Board-Folk/Einstein-TC-01/Kicad/einstein_addressing.kicad_sch

## KiCad design Kicad/einstein_addressing.kicad_sch (2025-11-02)

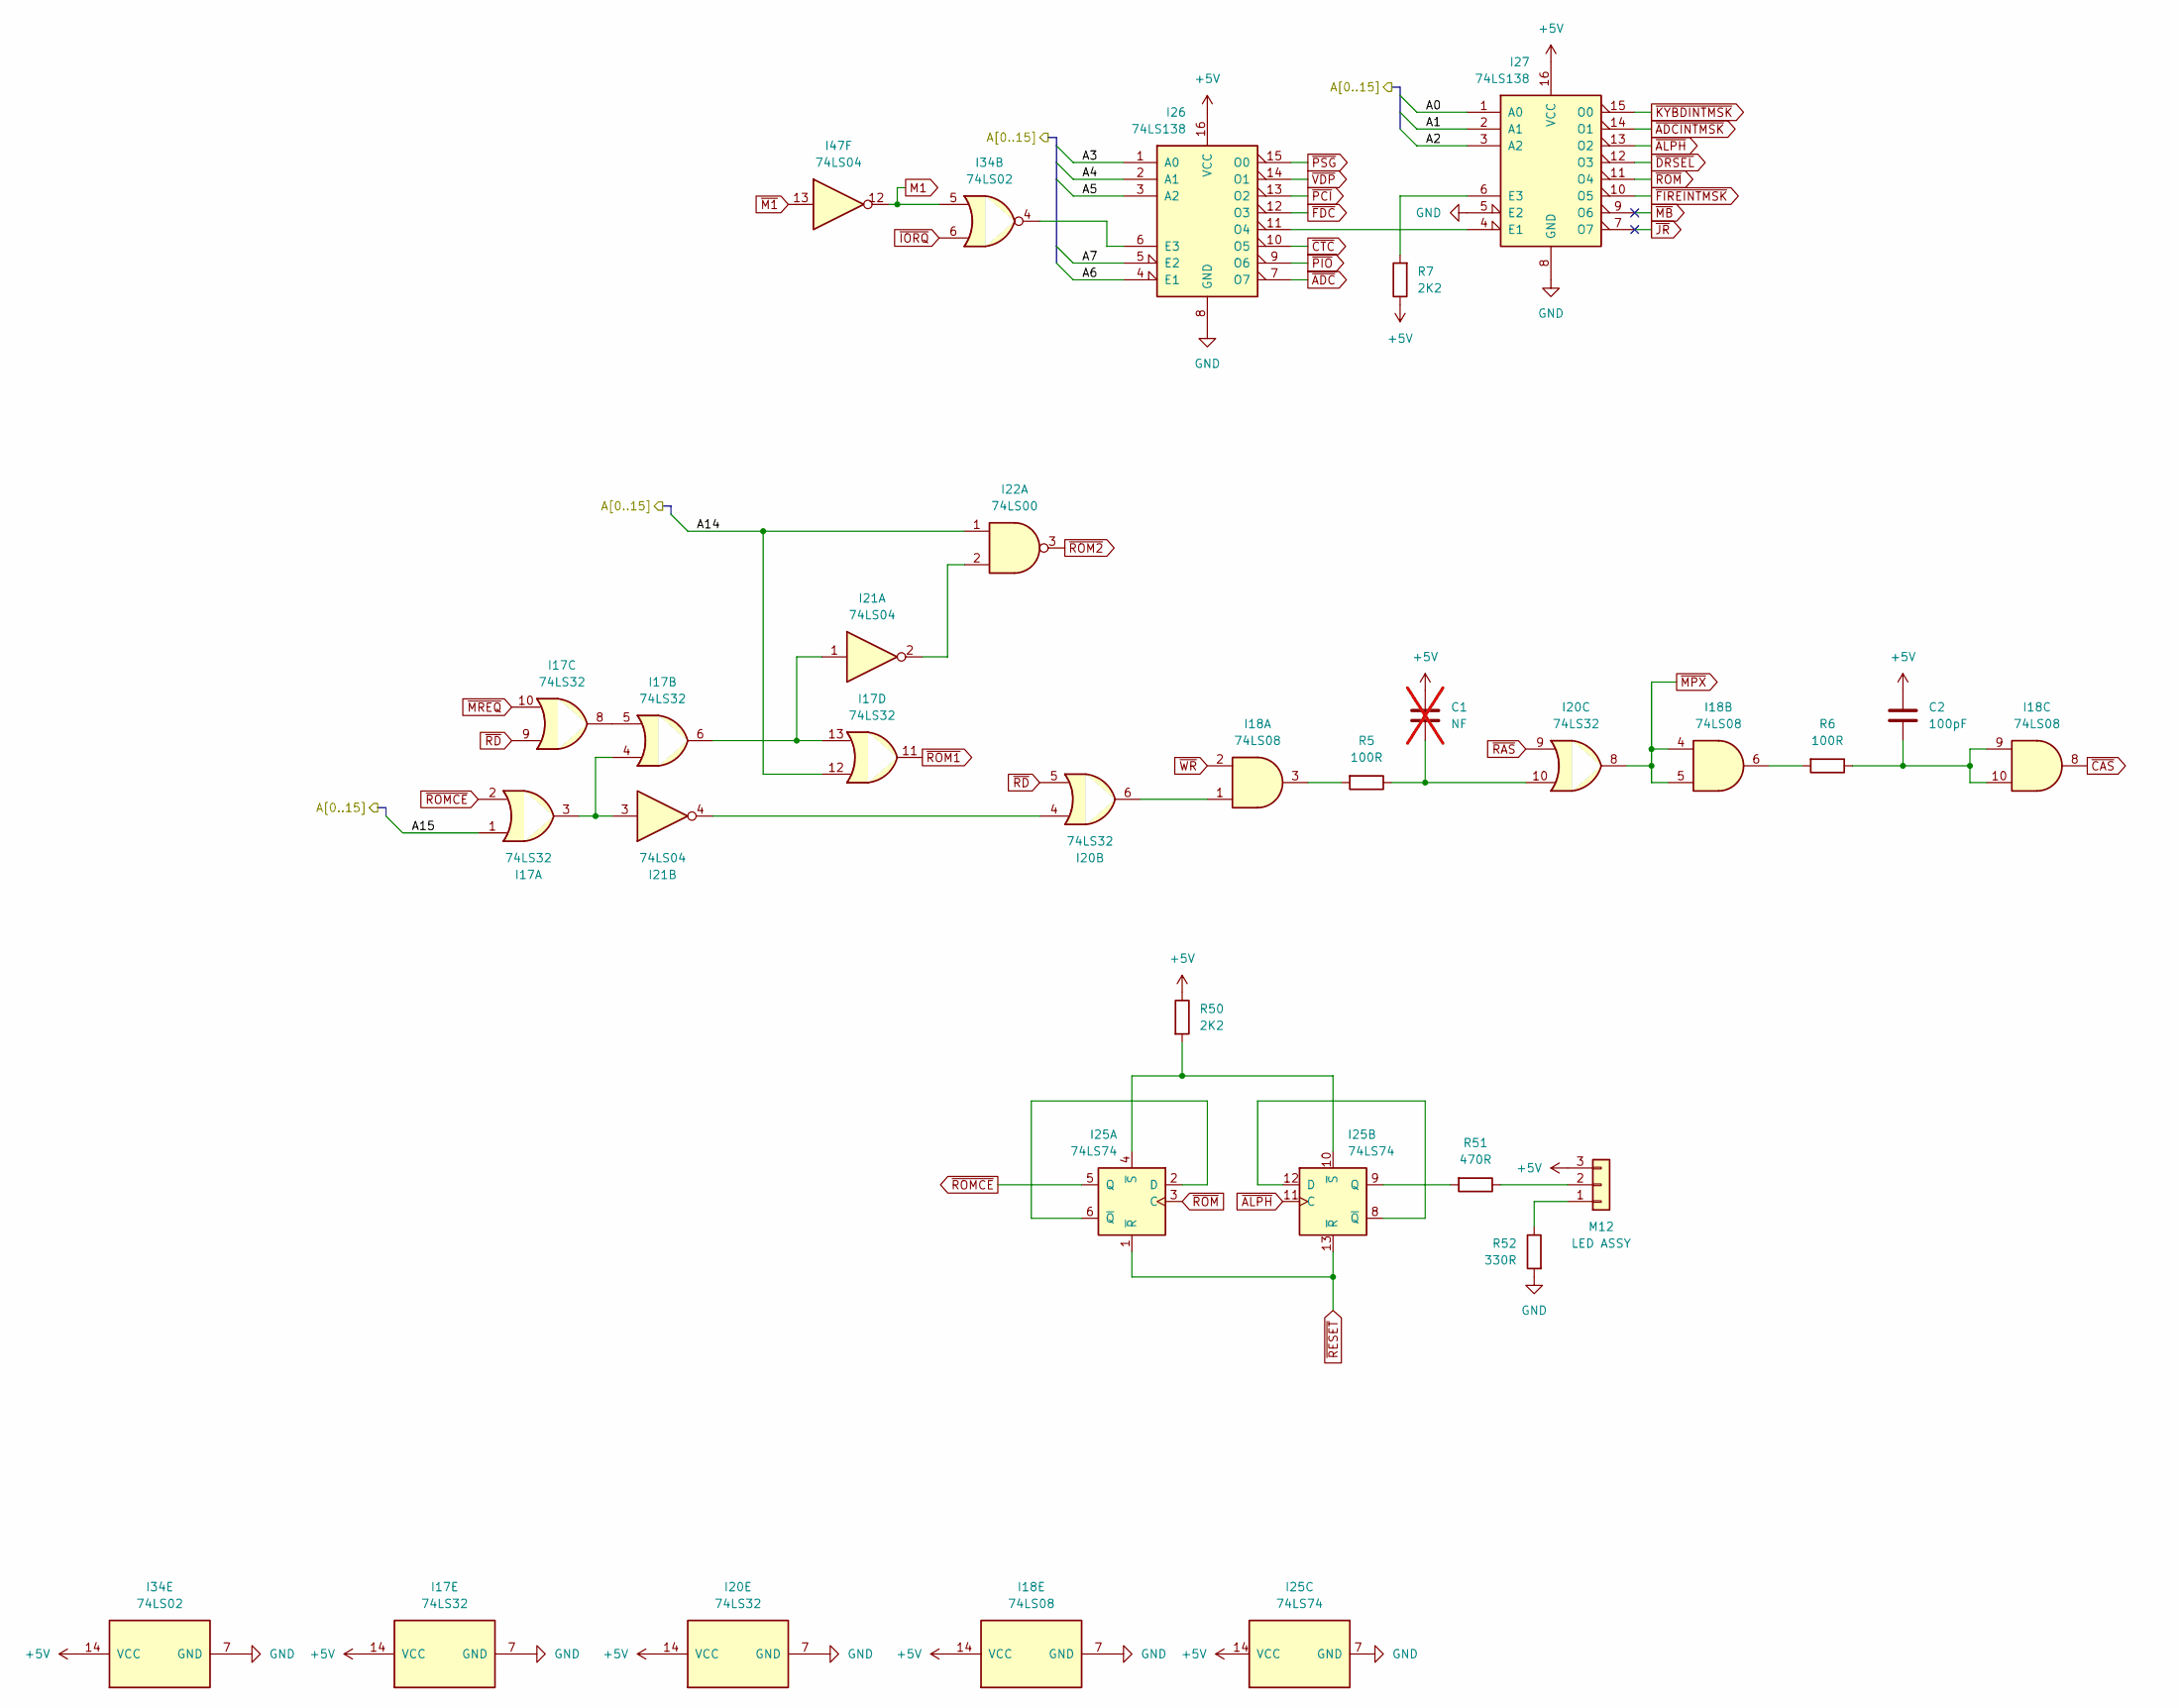
[picture p41: schematic einstein_addressing.kicad_sch]

Parts:
C1: NF; C_Disc_10.16mm; not fitted
C2: 100pF; C_Disc_10.16mm
I17, I20: 74LS32; DIP-14_W7.62mm
I18: 74LS08; DIP-14_W7.62mm
I21, I47: 74LS04; DIP-14_W7.62mm
I22: 74LS00; DIP-14_W7.62mm
I25: 74LS74; DIP-14_W7.62mm
I26, I27: 74LS138; DIP-16_W7.62mm
I34: 74LS02; DIP-14_W7.62mm
M12: LED ASSY; M12 PinHeader_1x03_P2.54mm
R5, R6: 100R; Resistor 12.70mm
R7, R50: 2K2; Resistor 12.70mm
R51: 470R; Resistor 12.70mm
R52: 330R; Resistor 12.70mm

Connections:
+5V: C1.1, C2.1, I17.14 (VCC), I18.14 (VCC), I20.14 (VCC), I25.14 (VCC), I26.16 (VCC), I27.16 (VCC), I34.14 (VCC), M12.3, R7.1, R50.1
A0: I27.1 (A0)
A1: I27.2 (A1)
A2: I27.3 (A2)
A3: I26.1 (A0)
A4: I26.2 (A1)
A5: I26.3 (A2)
A6: I26.4 (E1)
A7: I26.5 (E2)
A14: I17.12, I22.1
A15: I17.1
GND: I17.7 (GND), I18.7 (GND), I20.7 (GND), I25.7 (GND), I26.8 (GND), I27.5 (E2), I27.8 (GND), I34.7 (GND), R52.2
M1: I34.5, I47.12
unnamed: C1.2, I20.10, R5.1
unnamed: C2.2, I18.9, I18.10, R6.1
unnamed: I17.3, I17.4, I21.3
unnamed: I17.5, I17.8
unnamed: I17.6, I17.13, I21.1
unnamed: I18.1, I20.6
unnamed: I18.3, R5.2
unnamed: I18.6, R6.2
unnamed: I20.4, I21.4
unnamed: I21.2, I22.2
unnamed: I25.2 (D), I25.6 (~Q)
unnamed: I25.9 (Q), R51.2
unnamed: I25.4 (~S), I25.10 (~S), R50.2
unnamed: I25.8 (~Q), I25.12 (D)
unnamed: I26.6 (E3), I34.4
unnamed: I26.11 (O4), I27.4 (E1)
unnamed: I27.6 (E3), R7.2
unnamed: M12.1, R52.1
unnamed: M12.2, R51.1
~ADCINTMSK: I27.14 (O1)
~ADC: I26.7 (O7)
~ALPH: I25.11 (C), I27.13 (O2)
~CAS: I18.8
~CTC: I26.10 (O5)
~DRSEL: I27.12 (O3)
~FDC: I26.12 (O3)
~FIREINTMSK: I27.10 (O5)
~IORQ: I34.6
~JR: I27.7 (O7)
~KYBDINTMSK: I27.15 (O0)
~M1: I47.13
~MB: I27.9 (O6)
~MPX: I18.4, I18.5, I20.8
~MREQ: I17.10
~PCI: I26.13 (O2)
~PIO: I26.9 (O6)
~PSG: I26.15 (O0)
~RAS: I20.9
~RD: I17.9, I20.5
~RESET: I25.1 (~R), I25.13 (~R)
~ROM1: I17.11
~ROM2: I22.3
~ROMCE: I17.2, I25.5 (Q)
~ROM: I25.3 (C), I27.11 (O4)
~VDP: I26.14 (O1)
~WR: I18.2
