Board-Folk/Einstein-TC-01/Kicad/einstein_cpu.kicad_sch

## KiCad design Kicad/einstein_cpu.kicad_sch (2026-03-14)

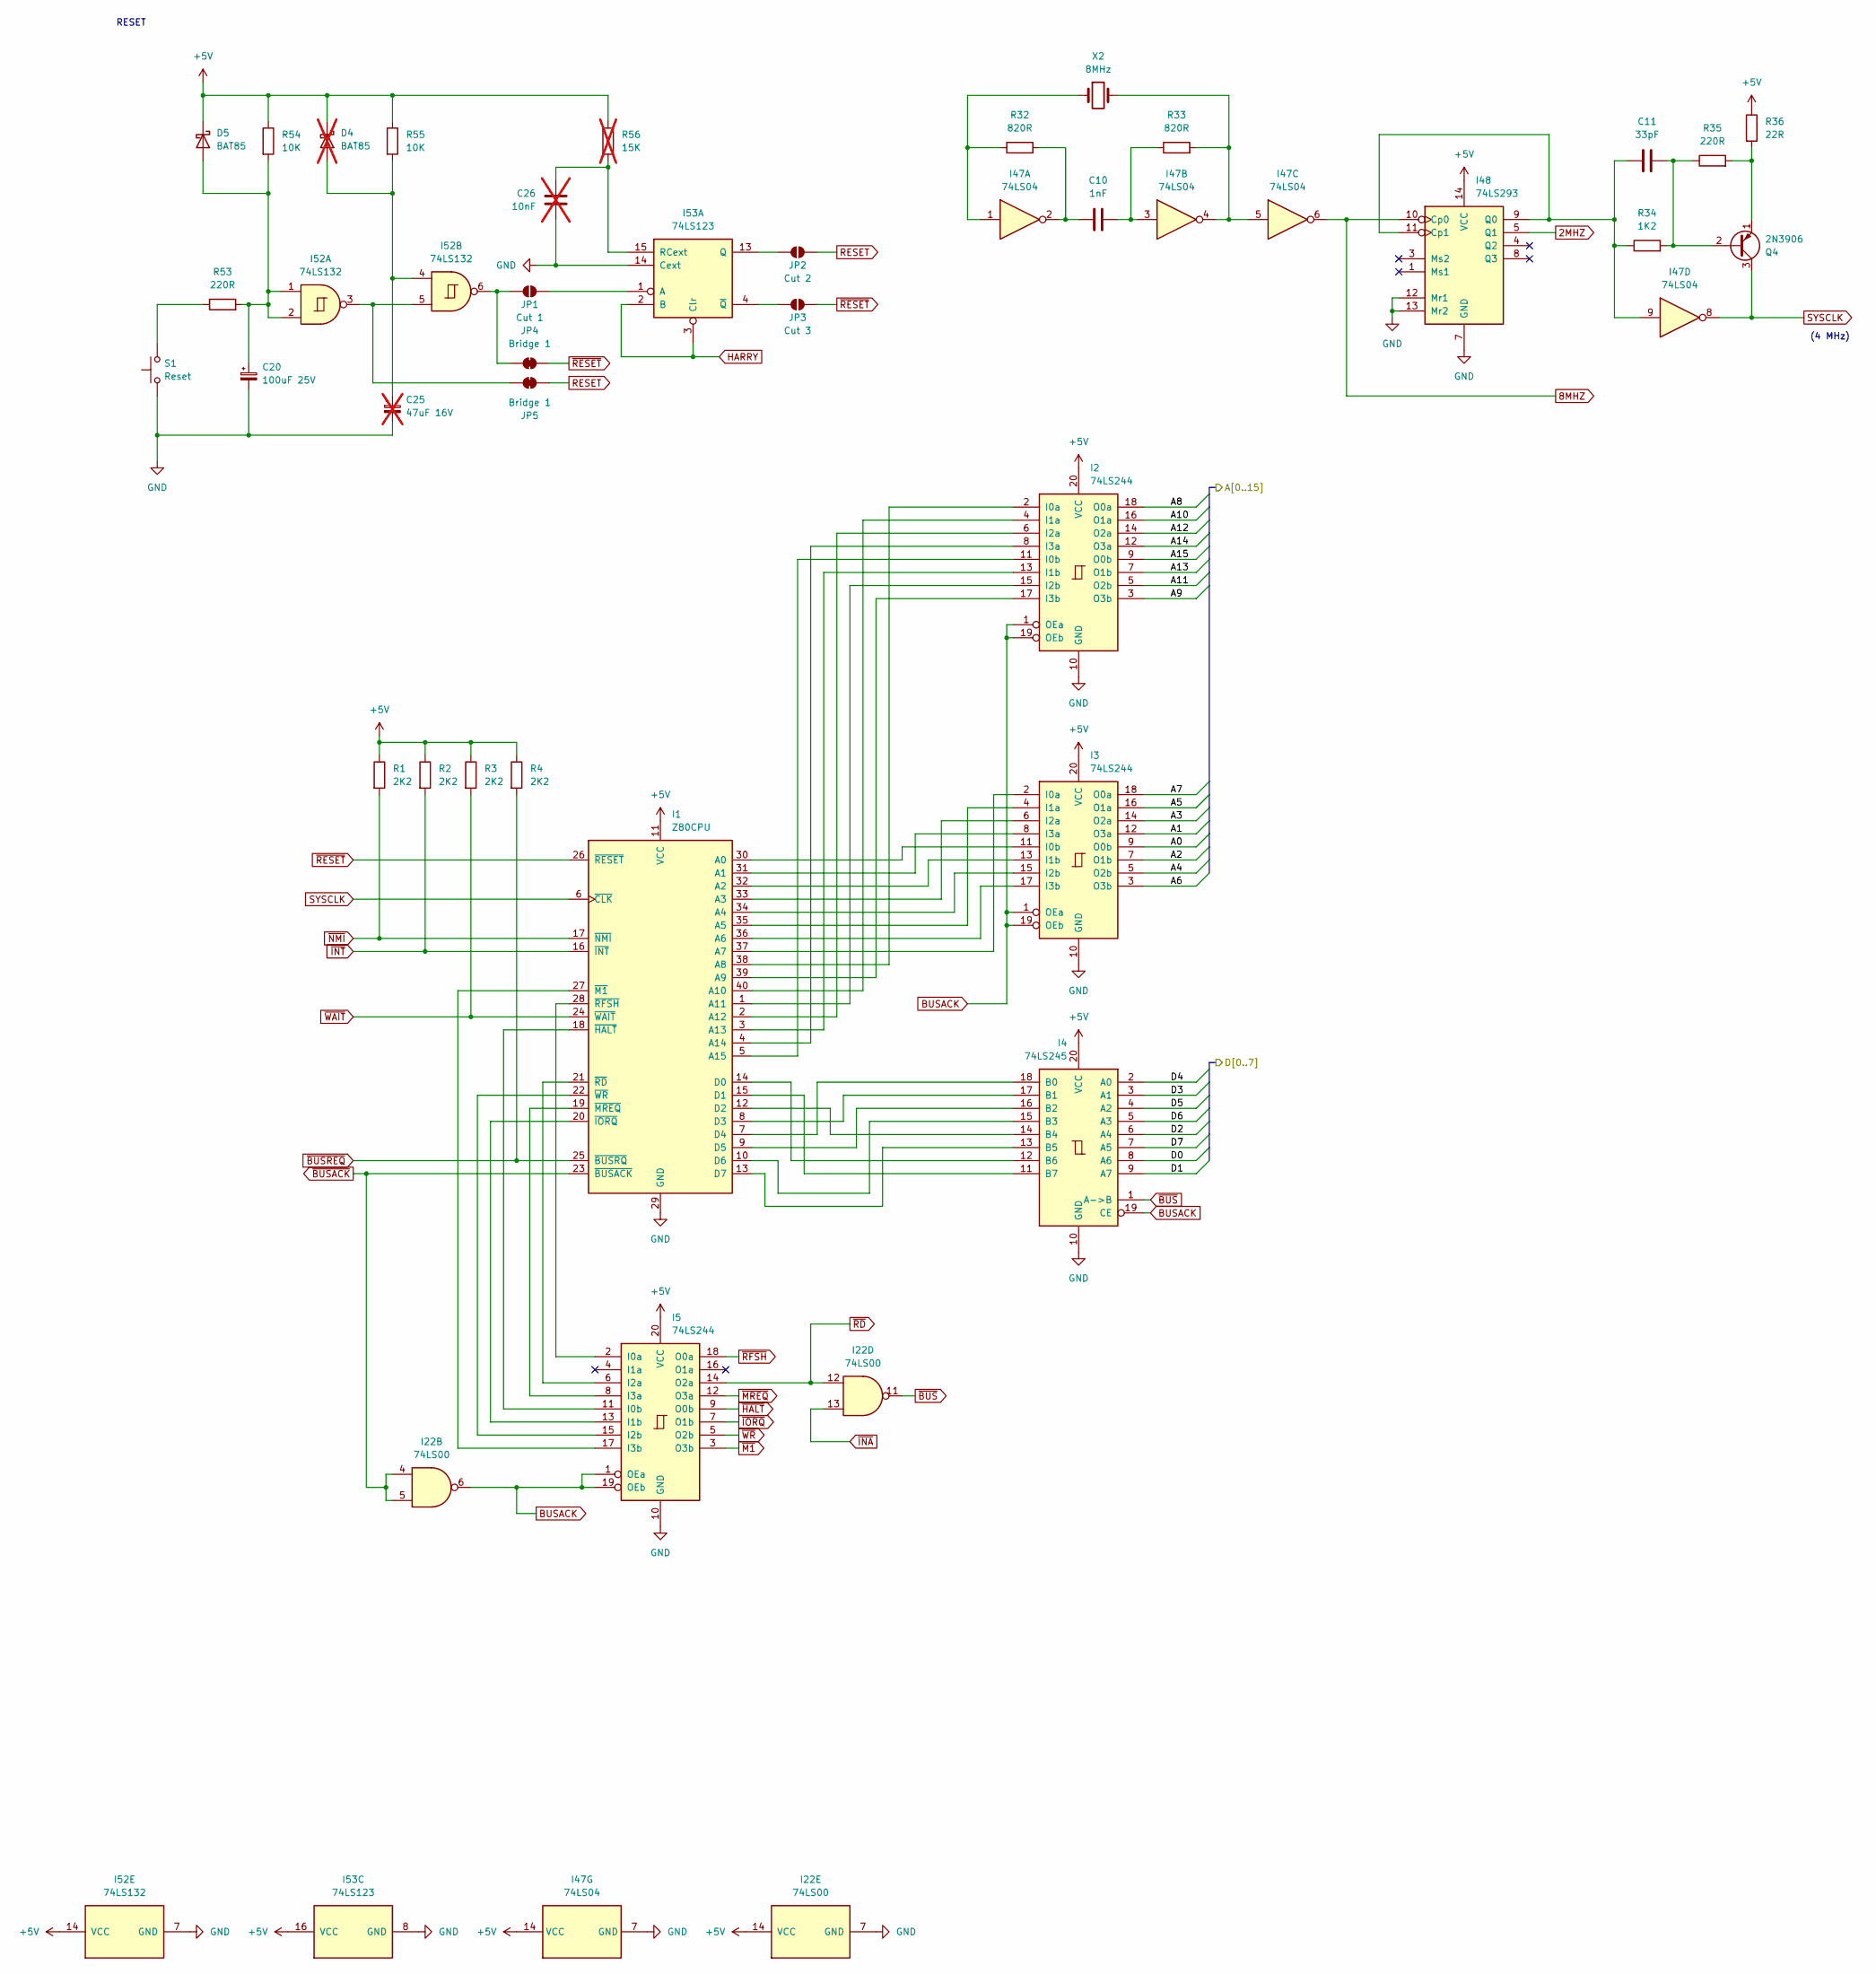
[picture p42: schematic einstein_cpu.kicad_sch]

Parts:
C10: 1nF; C_Disc_12.7mm
C11: 33pF; C_Disc_12.7mm
C20: 100uF 25V; Elec_5.08mm - Box
C25: 47uF 16V; Elec_5.08mm - Box; not fitted
C26: 10nF; C_Disc_12.7mm; not fitted
D4: BAT85; Diode 10.16mm; not fitted
D5: BAT85; Diode 10.16mm
I1: Z80CPU; DIP-40_W15.24mm
I2, I3, I5: 74LS244; DIP-20_W7.62mm
I4: 74LS245; DIP-20_W7.62mm
I22: 74LS00; DIP-14_W7.62mm
I47: 74LS04; DIP-14_W7.62mm
I48: 74LS293; DIP-14_W7.62mm
I52: 74LS132; DIP-14_W7.62mm
I53: 74LS123; DIP-16_W7.62mm
JP1: Cut 1; Bodge Cut
JP2: Cut 2; Bodge Cut
JP3: Cut 3; Bodge Cut
JP4, JP5: Bridge 1; Bodge Bridge
Q4: 2N3906; Transistor - Box 1 (Alt 1+3) No corner marking
R1, R2, R3, R4: 2K2; Resistor 12.70mm
R32, R33: 820R; Resistor 12.70mm
R34: 1K2; Resistor 12.70mm
R35, R53: 220R; Resistor 12.70mm
R36: 22R; Resistor 12.70mm
R54, R55: 10K; Resistor 12.70mm
R56: 15K; Resistor 12.70mm; not fitted
S1: Reset
X2: 8MHz; Crystal

Connections:
2MHZ: I48.5 (Q1)
8MHZ: I47.6, I48.10 (Cp0)
+5V: D4.1 (K), D5.1 (K), I1.11 (VCC), I2.20 (VCC), I3.20 (VCC), I4.20 (VCC), I5.20 (VCC), I22.14 (VCC), I47.14 (VCC), I48.14 (VCC), I52.14 (VCC), I53.16 (VCC), R1.1, R2.1, R3.1, R4.1, R36.1, R54.1, R55.1, R56.1
A0: I3.9 (O0b)
A1: I3.12 (O3a)
A2: I3.7 (O1b)
A3: I3.14 (O2a)
A4: I3.5 (O2b)
A5: I3.16 (O1a)
A6: I3.3 (O3b)
A7: I3.18 (O0a)
A8: I2.18 (O0a)
A9: I2.3 (O3b)
A10: I2.16 (O1a)
A11: I2.5 (O2b)
A12: I2.14 (O2a)
A13: I2.7 (O1b)
A14: I2.12 (O3a)
A15: I2.9 (O0b)
BUSACK: I2.1 (OEa), I2.19 (OEb), I3.1 (OEa), I3.19 (OEb), I4.19 (CE), I5.1 (OEa), I5.19 (OEb), I22.6
D0: I4.8 (A6)
D1: I4.9 (A7)
D2: I4.6 (A4)
D3: I4.3 (A1)
D4: I4.2 (A0)
D5: I4.4 (A2)
D6: I4.5 (A3)
D7: I4.7 (A5)
GND: C20.2, C25.2, C26.2, I1.29 (GND), I2.10 (GND), I3.10 (GND), I4.10 (GND), I5.10 (GND), I22.7 (GND), I47.7 (GND), I48.7 (GND), I48.12 (Mr1), I48.13 (Mr2), I52.7 (GND), I53.8 (GND), I53.14 (Cext), S1.1
HARRY: I53.2 (B), I53.3 (Clr)
unnamed: C10.1, I47.3, R33.1
unnamed: C10.2, I47.2, R32.2
unnamed: C11.1, Q4.2 (B), R34.2, R35.1
unnamed: C11.2, I47.9, I48.9 (Q0), I48.11 (Cp1), R34.1
unnamed: C20.1, D5.2 (A), I52.1, I52.2, R53.2, R54.2
unnamed: C25.1, D4.2 (A), I52.4, R55.2
unnamed: C26.1, I53.15 (RCext), R56.2
unnamed: I1.1 (A11), I2.15 (I2b)
unnamed: I1.2 (A12), I2.6 (I2a)
unnamed: I1.3 (A13), I2.13 (I1b)
unnamed: I1.4 (A14), I2.8 (I3a)
unnamed: I1.5 (A15), I2.11 (I0b)
unnamed: I1.7 (D4), I4.18 (B0)
unnamed: I1.8 (D3), I4.17 (B1)
unnamed: I1.9 (D5), I4.16 (B2)
unnamed: I1.10 (D6), I4.15 (B3)
unnamed: I1.12 (D2), I4.14 (B4)
unnamed: I1.13 (D7), I4.13 (B5)
unnamed: I1.14 (D0), I4.12 (B6)
unnamed: I1.15 (D1), I4.11 (B7)
unnamed: I1.18 (~HALT), I5.11 (I0b)
unnamed: I1.19 (~MREQ), I5.8 (I3a)
unnamed: I1.20 (~IORQ), I5.13 (I1b)
unnamed: I1.21 (~RD), I5.6 (I2a)
unnamed: I1.22 (~WR), I5.15 (I2b)
unnamed: I1.27 (~M1), I5.17 (I3b)
unnamed: I1.28 (~RFSH), I5.2 (I0a)
unnamed: I1.30 (A0), I3.11 (I0b)
unnamed: I1.31 (A1), I3.8 (I3a)
unnamed: I1.32 (A2), I3.13 (I1b)
unnamed: I1.33 (A3), I3.6 (I2a)
unnamed: I1.34 (A4), I3.15 (I2b)
unnamed: I1.35 (A5), I3.4 (I1a)
unnamed: I1.36 (A6), I3.17 (I3b)
unnamed: I1.37 (A7), I3.2 (I0a)
unnamed: I1.38 (A8), I2.2 (I0a)
unnamed: I1.39 (A9), I2.17 (I3b)
unnamed: I1.40 (A10), I2.4 (I1a)
unnamed: I47.1, R32.1, X2.1
unnamed: I47.4, I47.5, R33.2, X2.2
unnamed: I52.3, I52.5, JP5.1 (A)
unnamed: I52.6, JP1.1 (A), JP4.1 (A)
unnamed: I53.1 (A), JP1.2 (B)
unnamed: I53.4 (~Q), JP3.1 (A)
unnamed: I53.13 (Q), JP2.1 (A)
unnamed: Q4.1 (E), R35.2, R36.2
unnamed: R53.1, S1.2
RESET: JP2.2 (B), JP5.2 (B)
SYSCLK: I1.6 (~CLK), I47.8, Q4.3 (C)
~BUSACK: I1.23 (~BUSACK), I22.4, I22.5
~BUSREQ: I1.25 (~BUSRQ), R4.2
~BUS: I4.1 (A->B), I22.11
~HALT: I5.9 (O0b)
~INA: I22.13
~INT: I1.16 (~INT), R2.2
~IORQ: I5.7 (O1b)
~M1: I5.3 (O3b)
~MREQ: I5.12 (O3a)
~NMI: I1.17 (~NMI), R1.2
~RD: I5.14 (O2a), I22.12
~RESET: I1.26 (~RESET), JP3.2 (B), JP4.2 (B)
~RFSH: I5.18 (O0a)
~WAIT: I1.24 (~WAIT), R3.2
~WR: I5.5 (O2b)

Notes on the sheet:
(4 MHz)
RESET
