Board-Folk/Einstein-TC-01/Kicad/einstein_fdd.kicad_sch

## KiCad design Kicad/einstein_fdd.kicad_sch (2025-11-02)

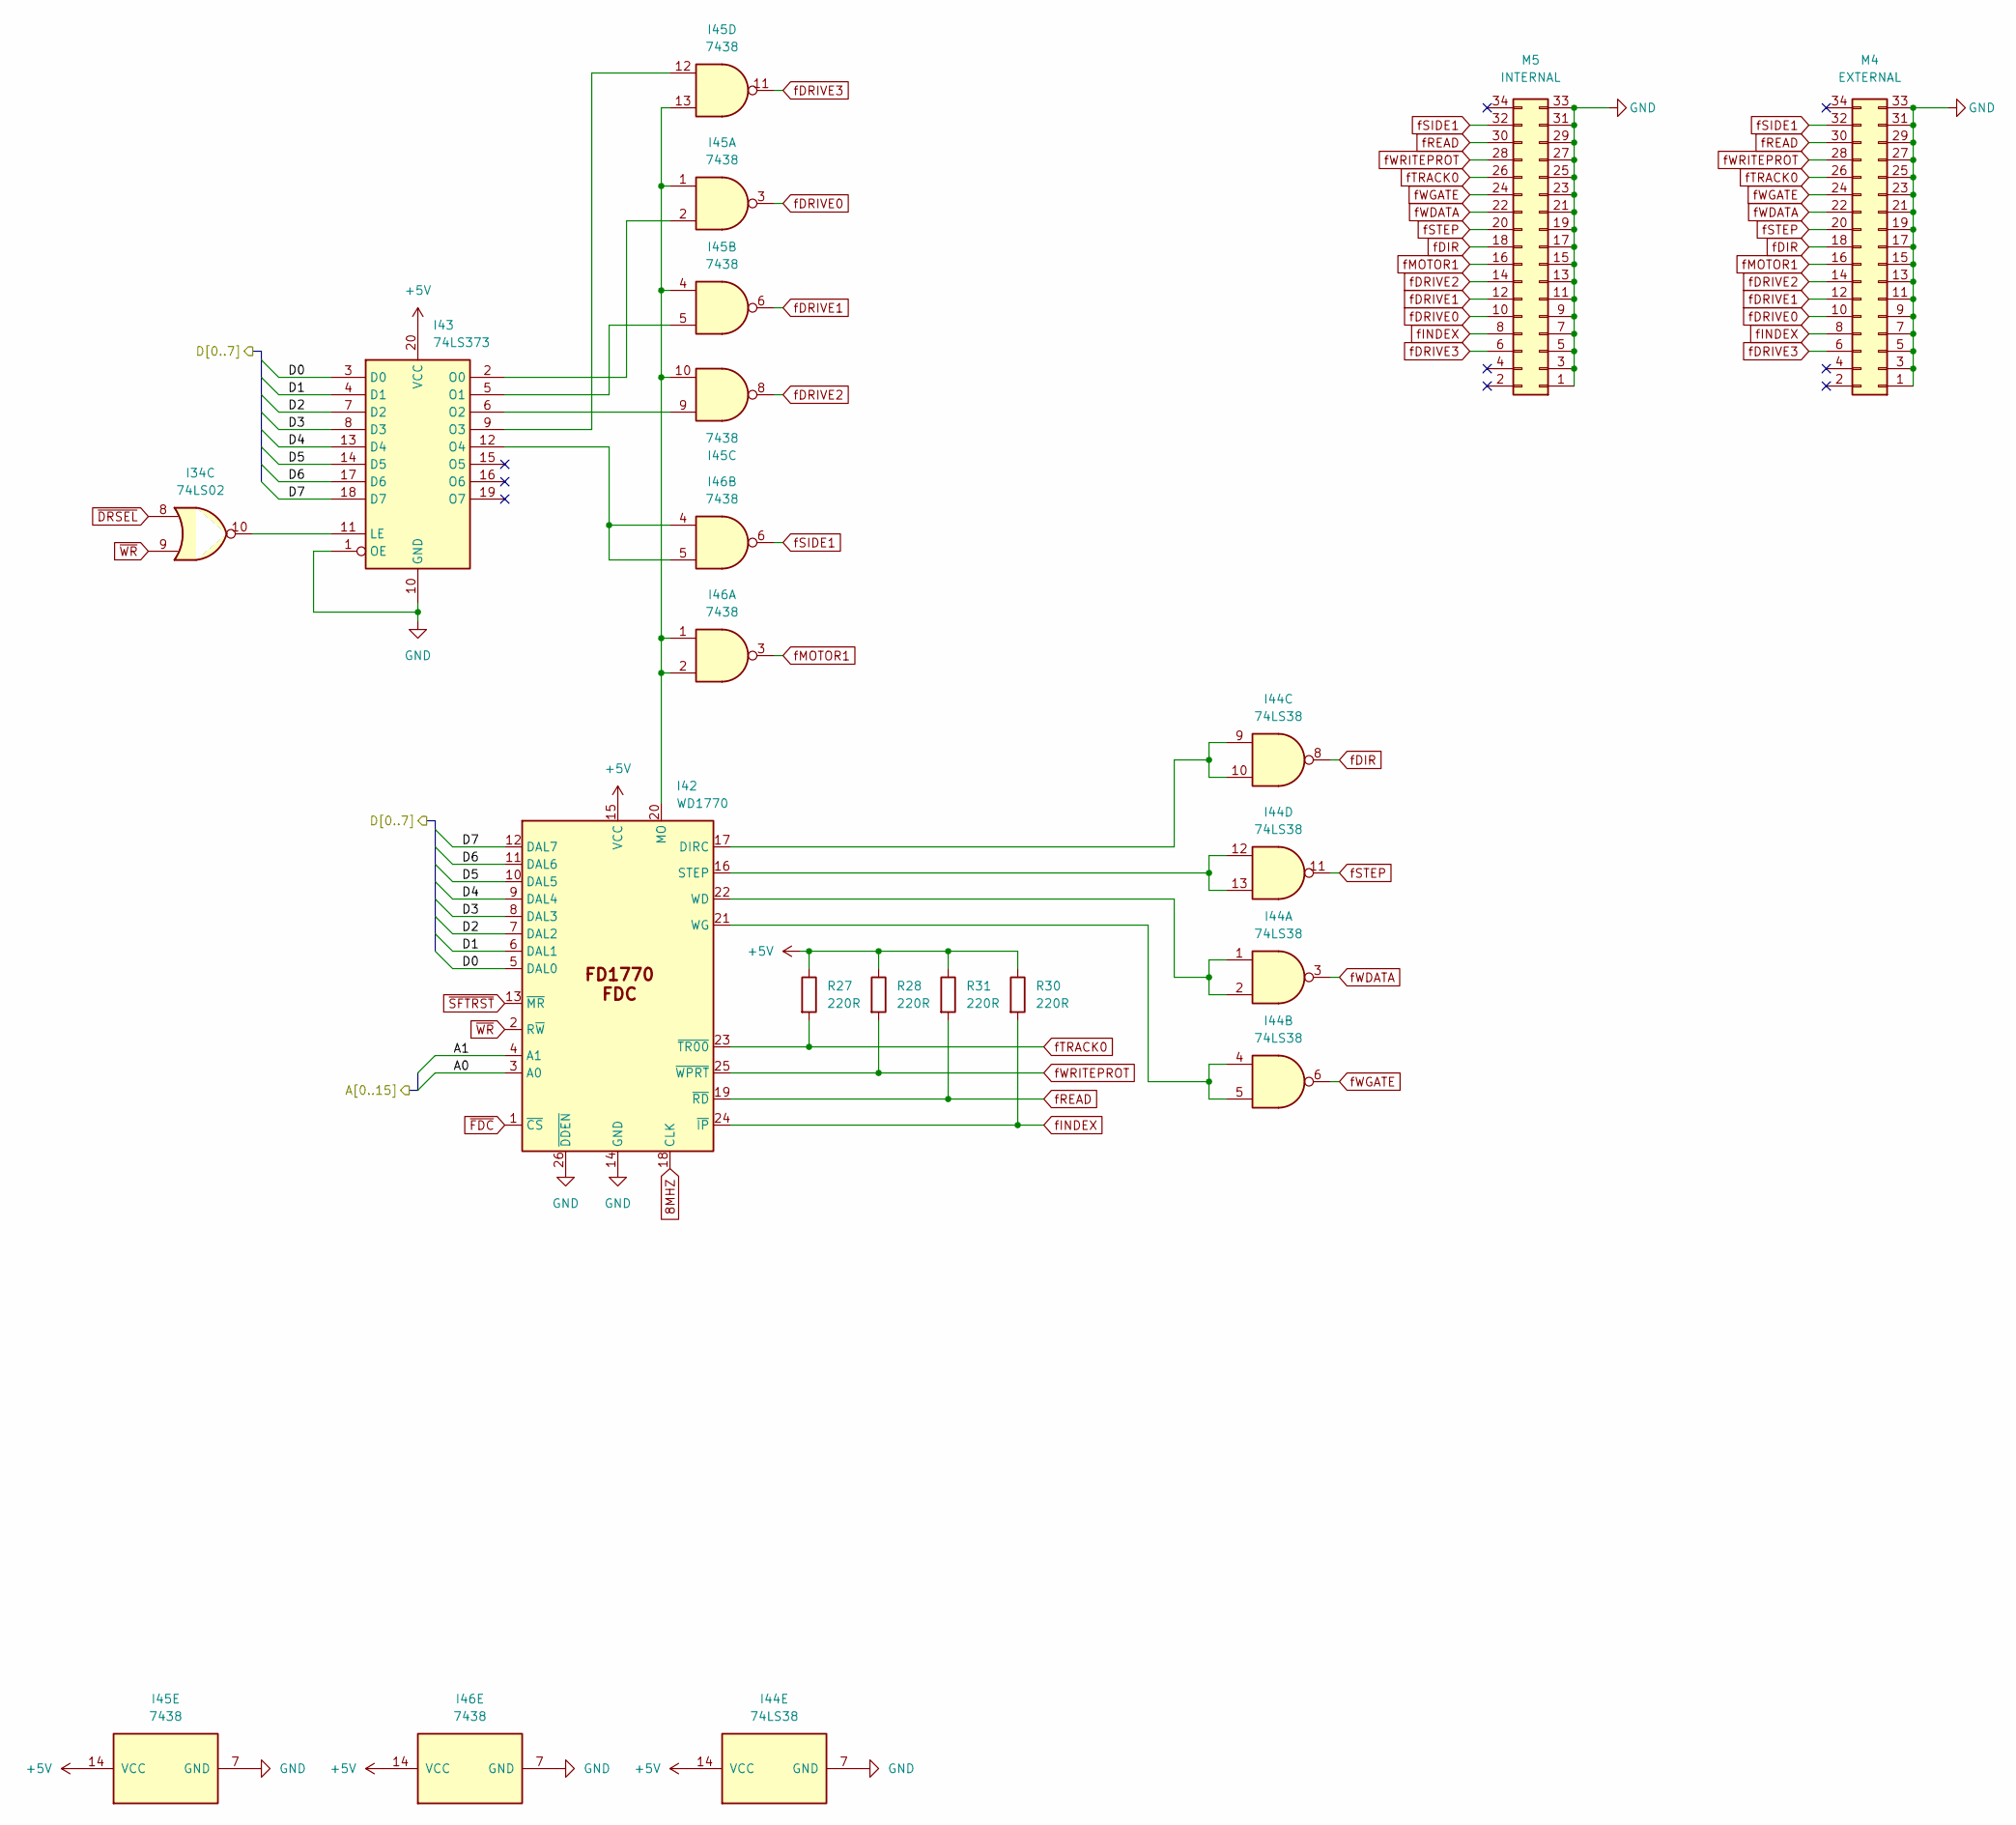
[picture p43: schematic einstein_fdd.kicad_sch]

Parts:
I34: 74LS02; DIP-14_W7.62mm
I42: WD1770; DIP-28_W15.24mm
I43: 74LS373; DIP-20_W7.62mm
I44: 74LS38; DIP-14_W7.62mm
I45, I46: 7438; DIP-14_W7.62mm
M4: EXTERNAL; PinHeader_2x17_P2.54mm
M5: INTERNAL; PinHeader_2x17_P2.54mm
R27, R28, R30, R31: 220R; Resistor 12.70mm

Connections:
8MHZ: I42.18 (CLK)
+5V: I42.15 (VCC), I43.20 (VCC), I44.14 (VCC), I45.14 (VCC), I46.14 (VCC), R27.1, R28.1, R30.1, R31.1
A0: I42.3 (A0)
A1: I42.4 (A1)
D0: I42.5 (DAL0), I43.3 (D0)
D1: I42.6 (DAL1), I43.4 (D1)
D2: I42.7 (DAL2), I43.7 (D2)
D3: I42.8 (DAL3), I43.8 (D3)
D4: I42.9 (DAL4), I43.13 (D4)
D5: I42.10 (DAL5), I43.14 (D5)
D6: I42.11 (DAL6), I43.17 (D6)
D7: I42.12 (DAL7), I43.18 (D7)
GND: I42.14 (GND), I42.26 (~DDEN), I43.1 (OE), I43.10 (GND), I44.7 (GND), I45.7 (GND), I46.7 (GND), M4.1, M4.3, M4.5, M4.7, M4.9, M4.11, M4.13, M4.15, M4.17, M4.19, M4.21, M4.23, M4.25, M4.27, M4.29, M4.31, M4.33, M5.1, M5.3, M5.5, M5.7, M5.9, M5.11, M5.13, M5.15, M5.17, M5.19, M5.21, M5.23, M5.25, M5.27, M5.29, M5.31, M5.33
unnamed: I34.10, I43.11 (LE)
unnamed: I42.16 (STEP), I44.12, I44.13
unnamed: I42.17 (DIRC), I44.9, I44.10
unnamed: I42.20 (MO), I45.1, I45.4, I45.10, I45.13, I46.1, I46.2
unnamed: I42.21 (WG), I44.4, I44.5
unnamed: I42.22 (WD), I44.1, I44.2
unnamed: I43.2 (O0), I45.2
unnamed: I43.5 (O1), I45.5
unnamed: I43.6 (O2), I45.9
unnamed: I43.9 (O3), I45.12
unnamed: I43.12 (O4), I46.4, I46.5
fDIR: I44.8, M4.18, M5.18
fDRIVE0: I45.3, M4.10, M5.10
fDRIVE1: I45.6, M4.12, M5.12
fDRIVE2: I45.8, M4.14, M5.14
fDRIVE3: I45.11, M4.6, M5.6
fINDEX: I42.24 (~IP), M4.8, M5.8, R30.2
fMOTOR1: I46.3, M4.16, M5.16
fREAD: I42.19 (~RD), M4.30, M5.30, R31.2
fSIDE1: I46.6, M4.32, M5.32
fSTEP: I44.11, M4.20, M5.20
fTRACK0: I42.23 (~TR00), M4.26, M5.26, R27.2
fWDATA: I44.3, M4.22, M5.22
fWGATE: I44.6, M4.24, M5.24
fWRITEPROT: I42.25 (~WPRT), M4.28, M5.28, R28.2
~DRSEL: I34.8
~FDC: I42.1 (~CS)
~SFTRST: I42.13 (~MR)
~WR: I34.9, I42.2 (R~W)
