Board-Folk/Einstein-TC-01/Kicad/einstein_memory.kicad_sch

## KiCad design Kicad/einstein_memory.kicad_sch (2025-11-02)

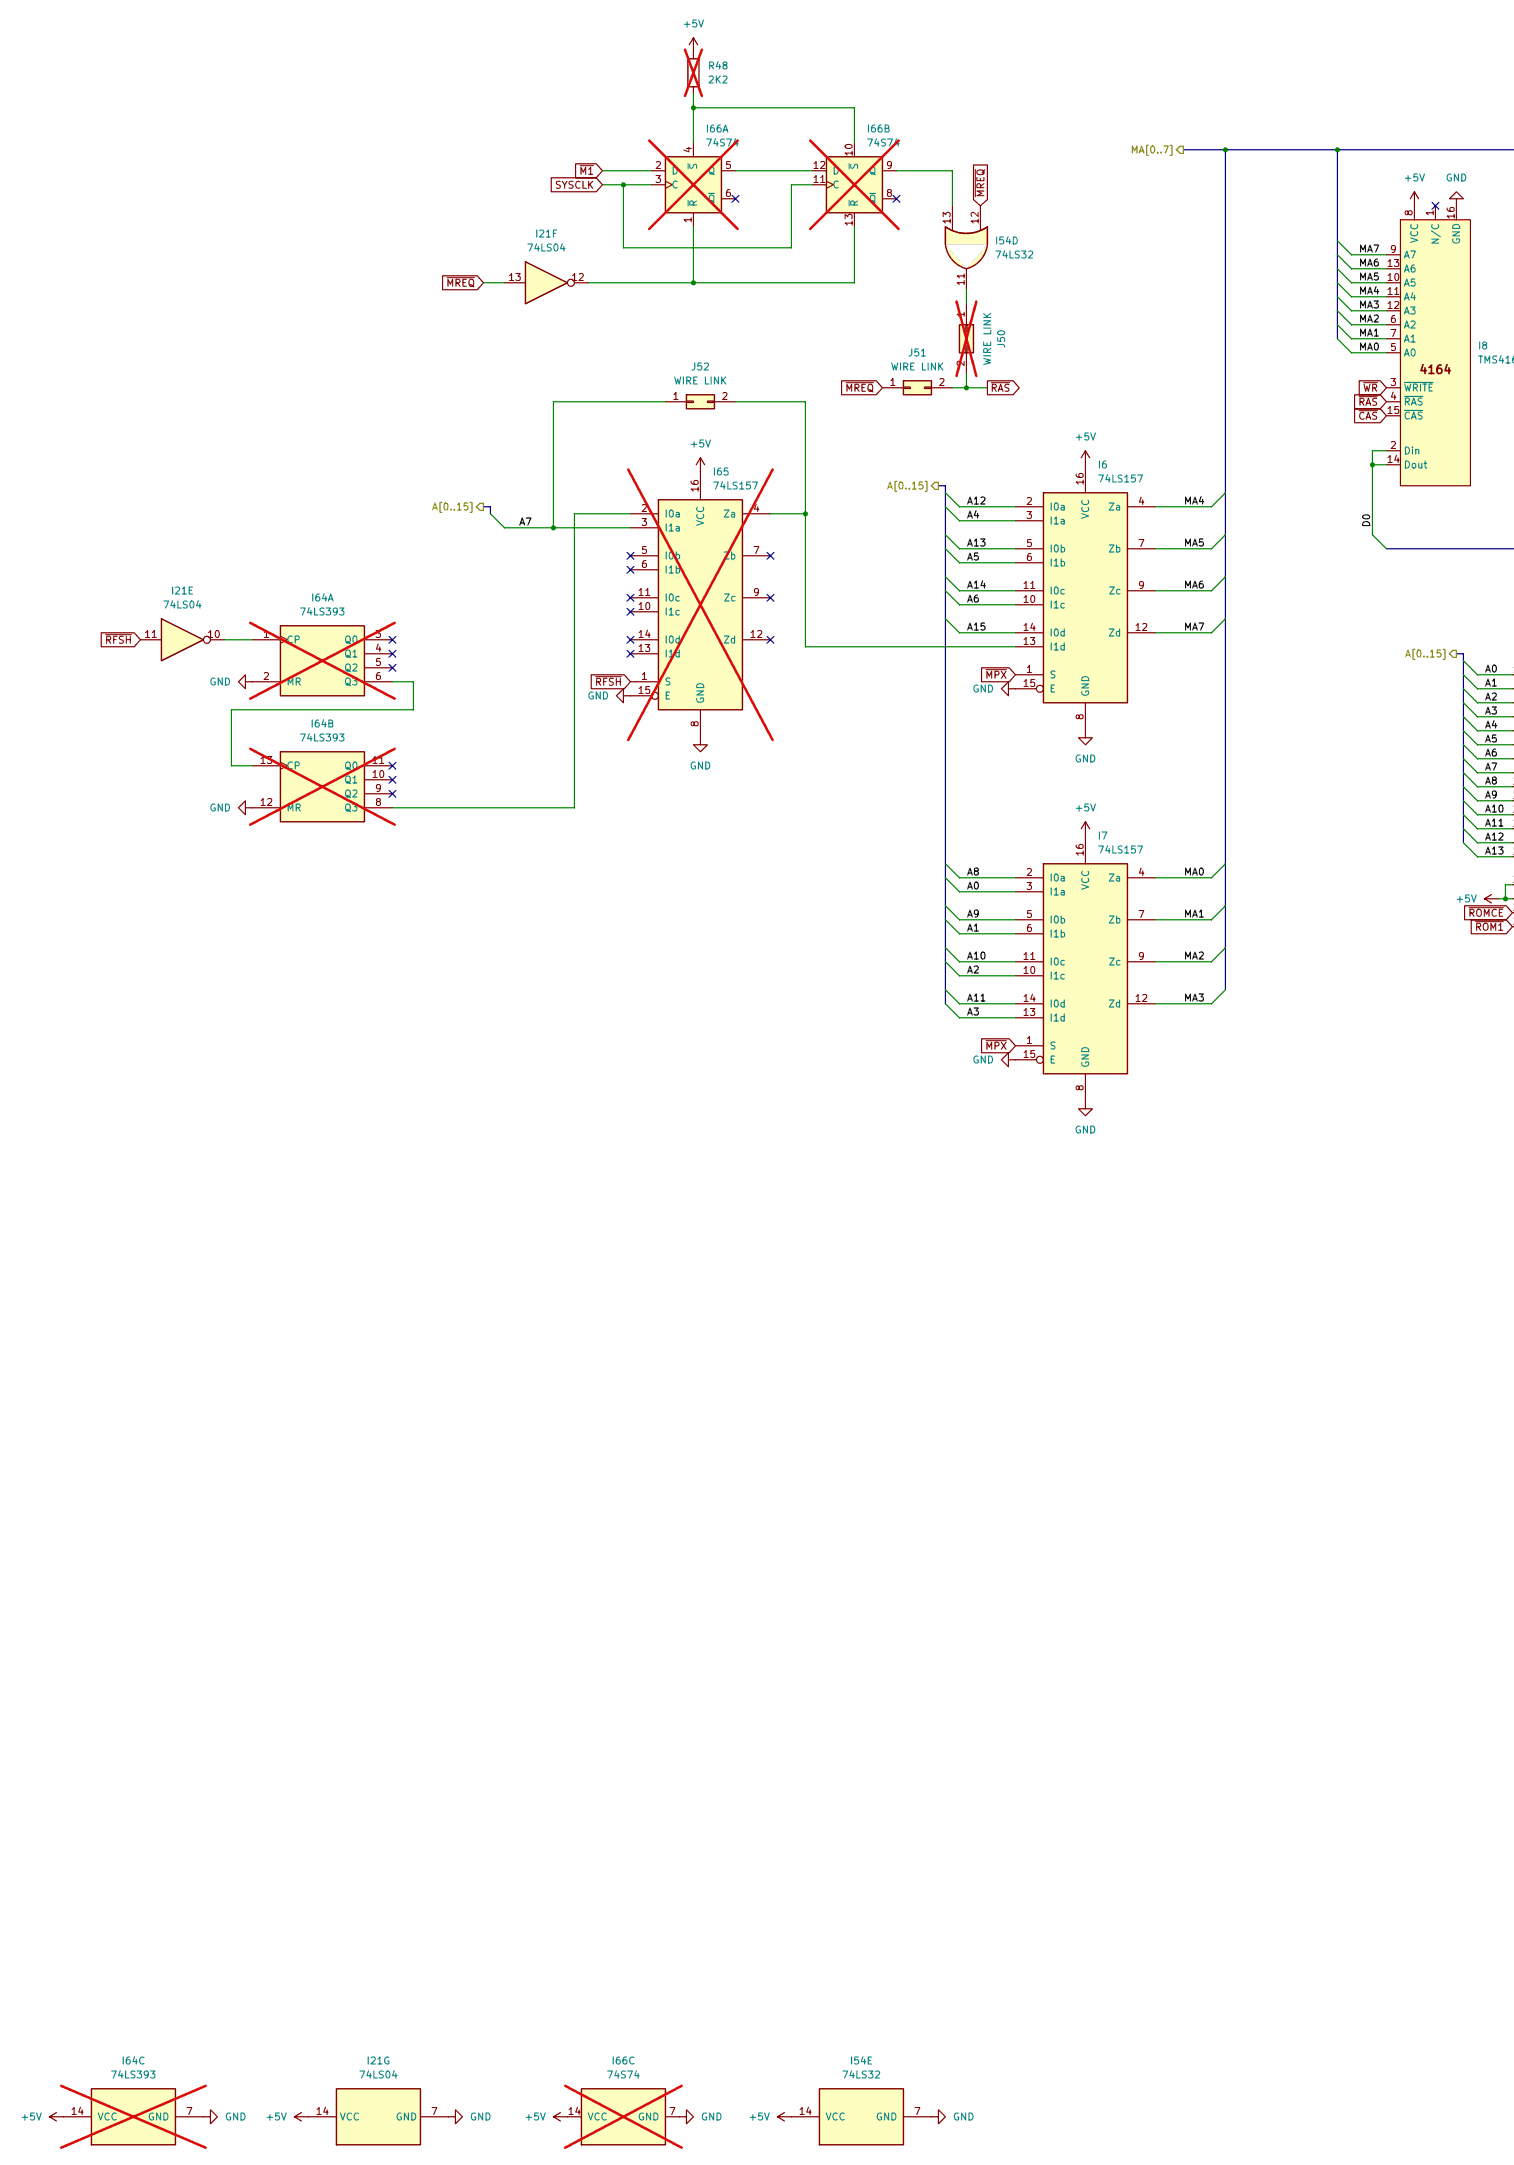
[picture p44: schematic einstein_memory.kicad_sch, part in row 1, column 1]

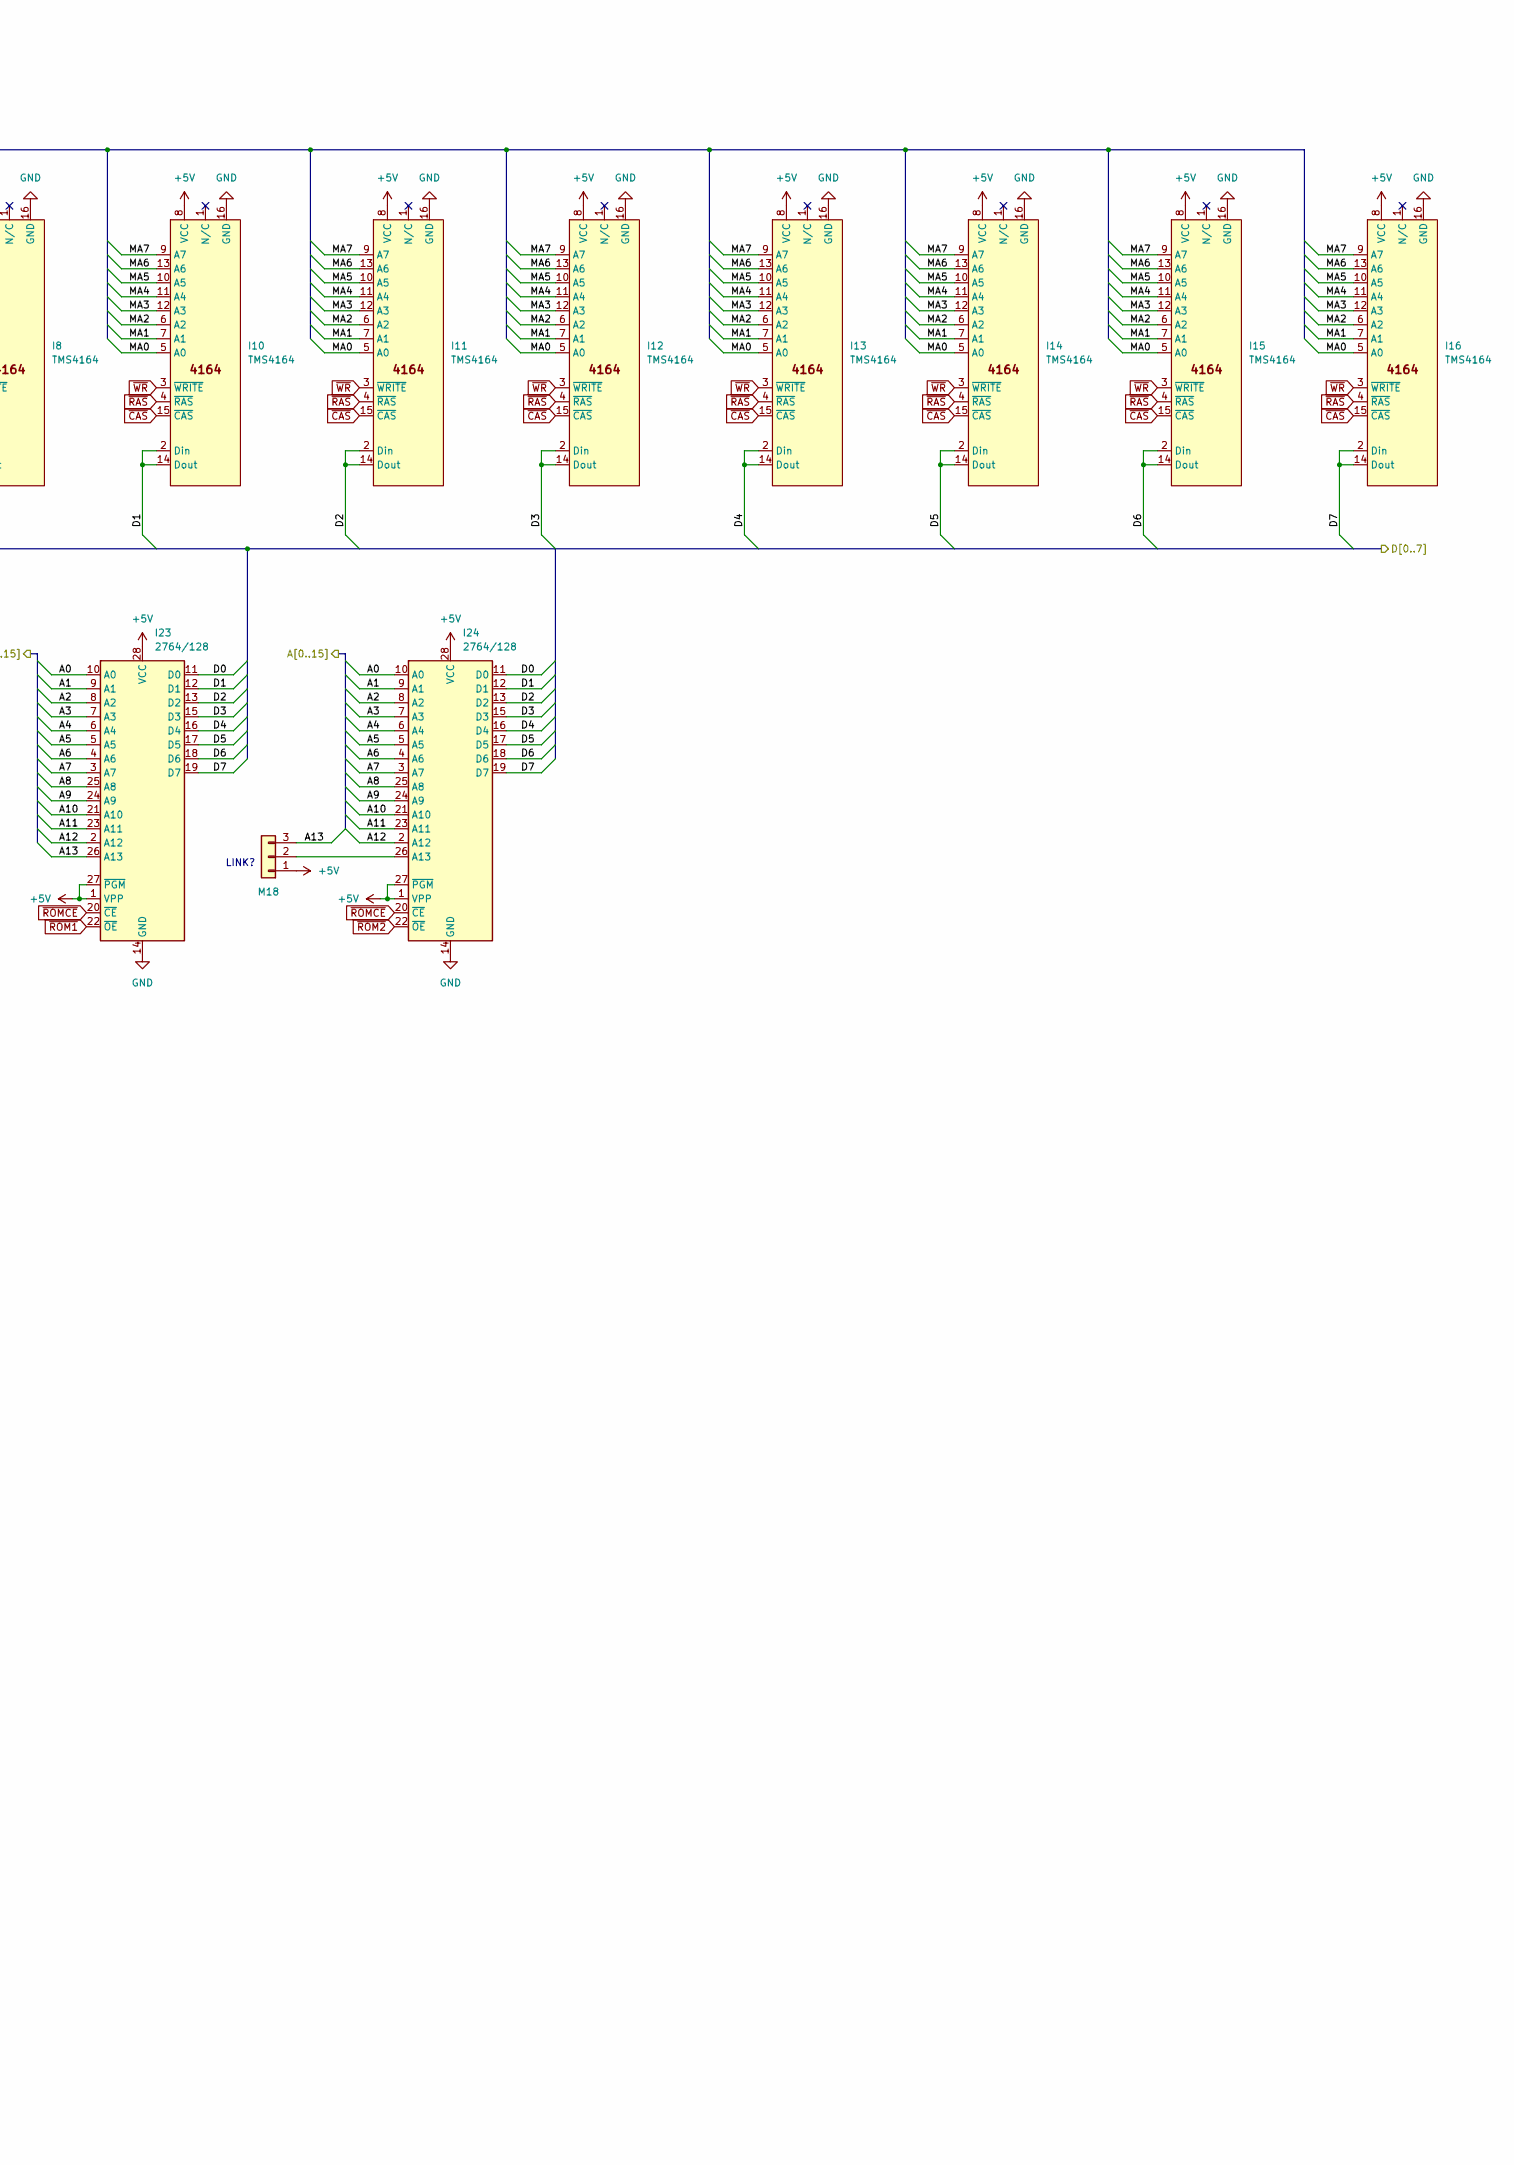
[picture p45: schematic einstein_memory.kicad_sch, part in row 1, column 2]

Parts:
I6, I7: 74LS157; DIP-16_W7.62mm
I8, I10, I11, I12, I13, I14, I15, I16: TMS4164; DIP-16_W7.62mm
I21: 74LS04; DIP-14_W7.62mm
I23, I24: 2764/128; DIP-28_W15.24mm
I54: 74LS32; DIP-14_W7.62mm
I64: 74LS393; DIP-14_W7.62mm; not fitted
I65: 74LS157; DIP-16_W7.62mm; not fitted
I66: 74S74; DIP-14_W7.62mm; not fitted
J50: WIRE LINK; Wire_Link_8.96mm; not fitted
J51, J52: WIRE LINK; Wire_Link_8.96mm
M18: ROM; M18 PinHeader_1x03_P2.54mm
R48: 2K2; Resistor 12.70mm; not fitted

Connections:
+5V: I6.16 (VCC), I7.16 (VCC), I8.8 (VCC), I10.8 (VCC), I11.8 (VCC), I12.8 (VCC), I13.8 (VCC), I14.8 (VCC), I15.8 (VCC), I16.8 (VCC), I21.14 (VCC), I23.1 (VPP), I23.27 (~PGM), I23.28 (VCC), I24.1 (VPP), I24.27 (~PGM), I24.28 (VCC), I54.14 (VCC), I64.14 (VCC), I65.16 (VCC), I66.14 (VCC), M18.1, R48.1
A0: I7.3 (I1a), I23.10 (A0), I24.10 (A0)
A1: I7.6 (I1b), I23.9 (A1), I24.9 (A1)
A2: I7.10 (I1c), I23.8 (A2), I24.8 (A2)
A3: I7.13 (I1d), I23.7 (A3), I24.7 (A3)
A4: I6.3 (I1a), I23.6 (A4), I24.6 (A4)
A5: I6.6 (I1b), I23.5 (A5), I24.5 (A5)
A6: I6.10 (I1c), I23.4 (A6), I24.4 (A6)
A7: I23.3 (A7), I24.3 (A7), I65.3 (I1a), J52.1
A8: I7.2 (I0a), I23.25 (A8), I24.25 (A8)
A9: I7.5 (I0b), I23.24 (A9), I24.24 (A9)
A10: I7.11 (I0c), I23.21 (A10), I24.21 (A10)
A11: I7.14 (I0d), I23.23 (A11), I24.23 (A11)
A12: I6.2 (I0a), I23.2 (A12), I24.2 (A12)
A13: I6.5 (I0b), I23.26 (A13), M18.3
A14: I6.11 (I0c)
A15: I6.14 (I0d)
D0: I8.2 (Din), I8.14 (Dout), I23.11 (D0), I24.11 (D0)
D1: I10.2 (Din), I10.14 (Dout), I23.12 (D1), I24.12 (D1)
D2: I11.2 (Din), I11.14 (Dout), I23.13 (D2), I24.13 (D2)
D3: I12.2 (Din), I12.14 (Dout), I23.15 (D3), I24.15 (D3)
D4: I13.2 (Din), I13.14 (Dout), I23.16 (D4), I24.16 (D4)
D5: I14.2 (Din), I14.14 (Dout), I23.17 (D5), I24.17 (D5)
D6: I15.2 (Din), I15.14 (Dout), I23.18 (D6), I24.18 (D6)
D7: I16.2 (Din), I16.14 (Dout), I23.19 (D7), I24.19 (D7)
GND: I6.8 (GND), I6.15 (E), I7.8 (GND), I7.15 (E), I8.16 (GND), I10.16 (GND), I11.16 (GND), I12.16 (GND), I13.16 (GND), I14.16 (GND), I15.16 (GND), I16.16 (GND), I21.7 (GND), I23.14 (GND), I24.14 (GND), I54.7 (GND), I64.2 (MR), I64.7 (GND), I64.12 (MR), I65.8 (GND), I65.15 (E), I66.7 (GND)
MA0: I7.4 (Za), I8.5 (A0), I10.5 (A0), I11.5 (A0), I12.5 (A0), I13.5 (A0), I14.5 (A0), I15.5 (A0), I16.5 (A0)
MA1: I7.7 (Zb), I8.7 (A1), I10.7 (A1), I11.7 (A1), I12.7 (A1), I13.7 (A1), I14.7 (A1), I15.7 (A1), I16.7 (A1)
MA2: I7.9 (Zc), I8.6 (A2), I10.6 (A2), I11.6 (A2), I12.6 (A2), I13.6 (A2), I14.6 (A2), I15.6 (A2), I16.6 (A2)
MA3: I7.12 (Zd), I8.12 (A3), I10.12 (A3), I11.12 (A3), I12.12 (A3), I13.12 (A3), I14.12 (A3), I15.12 (A3), I16.12 (A3)
MA4: I6.4 (Za), I8.11 (A4), I10.11 (A4), I11.11 (A4), I12.11 (A4), I13.11 (A4), I14.11 (A4), I15.11 (A4), I16.11 (A4)
MA5: I6.7 (Zb), I8.10 (A5), I10.10 (A5), I11.10 (A5), I12.10 (A5), I13.10 (A5), I14.10 (A5), I15.10 (A5), I16.10 (A5)
MA6: I6.9 (Zc), I8.13 (A6), I10.13 (A6), I11.13 (A6), I12.13 (A6), I13.13 (A6), I14.13 (A6), I15.13 (A6), I16.13 (A6)
MA7: I6.12 (Zd), I8.9 (A7), I10.9 (A7), I11.9 (A7), I12.9 (A7), I13.9 (A7), I14.9 (A7), I15.9 (A7), I16.9 (A7)
unnamed: I6.13 (I1d), I65.4 (Za), J52.2
unnamed: I21.10, I64.1 (CP)
unnamed: I21.12, I66.1 (~R), I66.13 (~R)
unnamed: I24.26 (A13), M18.2
unnamed: I54.11, J50.1
unnamed: I54.13, I66.9 (Q)
unnamed: I64.8 (Q3), I65.2 (I0a)
unnamed: I64.6 (Q3), I64.13 (CP)
unnamed: I66.4 (~S), I66.10 (~S), R48.2
unnamed: I66.5 (Q), I66.12 (D)
SYSCLK: I66.3 (C), I66.11 (C)
~CAS: I8.15 (~CAS), I10.15 (~CAS), I11.15 (~CAS), I12.15 (~CAS), I13.15 (~CAS), I14.15 (~CAS), I15.15 (~CAS), I16.15 (~CAS)
~M1: I66.2 (D)
~MPX: I6.1 (S), I7.1 (S)
~MREQ: I21.13, I54.12, J51.1
~RAS: I8.4 (~RAS), I10.4 (~RAS), I11.4 (~RAS), I12.4 (~RAS), I13.4 (~RAS), I14.4 (~RAS), I15.4 (~RAS), I16.4 (~RAS), J50.2, J51.2
~RFSH: I21.11, I65.1 (S)
~ROM1: I23.22 (~OE)
~ROM2: I24.22 (~OE)
~ROMCE: I23.20 (~CE), I24.20 (~CE)
~WR: I8.3 (~WRITE), I10.3 (~WRITE), I11.3 (~WRITE), I12.3 (~WRITE), I13.3 (~WRITE), I14.3 (~WRITE), I15.3 (~WRITE), I16.3 (~WRITE)

Notes on the sheet:
LINK?
