Board-Folk/Einstein-TC-01/Kicad/einstein_power.kicad_sch

## KiCad design Kicad/einstein_power.kicad_sch (2025-11-02)

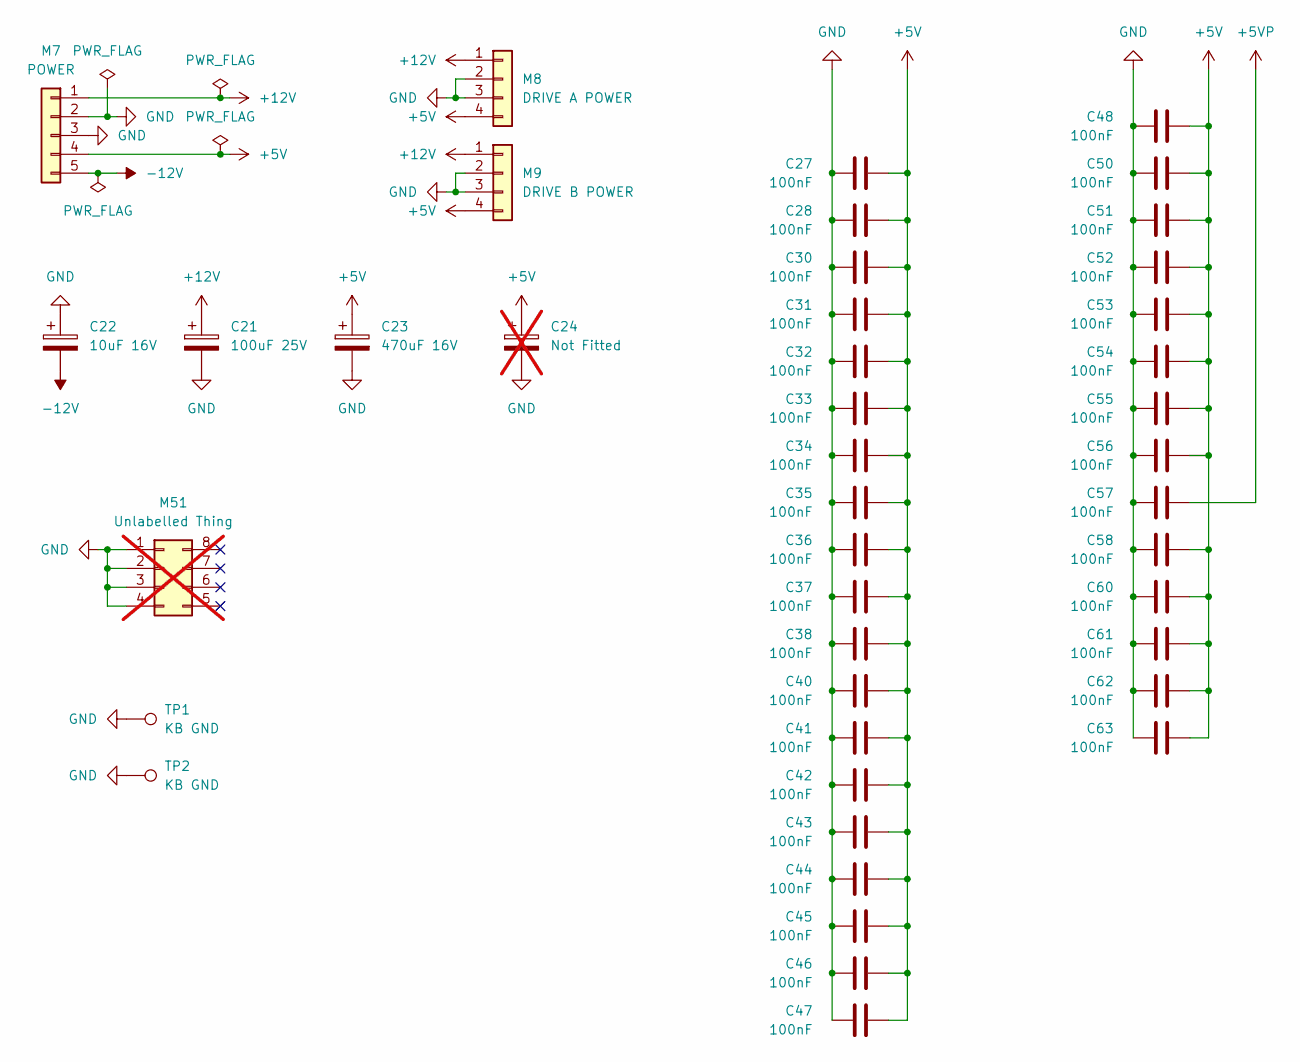
[picture p46: schematic einstein_power.kicad_sch]

Parts:
C21: 100uF 25V; Elec_5.08mm - Big Box
C22: 10uF 16V; Elec_5.08mm - Box
C23: 470uF 16V; Elec_5.08mm - Big Box
C24: Not Fitted; Elec_5.08mm - Big Box; not fitted
C27, C28, C30, C31, C32, C33, C34, C35, C36, C37, C38, C40, C41, C42, C43, C44, C45, C46, C47, C48, C50, C51, C52, C53, C54, C55, C56, C57, C58, C60, C61, C62, C63: 100nF; C_Disc_10.16mm
M7: POWER; Power 5
M8: DRIVE A POWER; Power 4
M9: DRIVE B POWER; Power 4
M51: Unlabelled Thing; Thing; not fitted
TP1, TP2: KB GND; TestPoint_THTPad_D1.0mm_Drill0.5mm

Connections:
+5V: C23.1, C24.1, C27.2, C28.2, C30.2, C31.2, C32.2, C33.2, C34.2, C35.2, C36.2, C37.2, C38.2, C40.2, C41.2, C42.2, C43.2, C44.2, C45.2, C46.2, C47.2, C48.2, C50.2, C51.2, C52.2, C53.2, C54.2, C55.2, C56.2, C58.2, C60.2, C61.2, C62.2, C63.2, M7.4, M8.4, M9.4
+5VP: C57.2
+12V: C21.1, M7.1, M8.1, M9.1
-12V: C22.2, M7.5
GND: C21.2, C22.1, C23.2, C24.2, C27.1, C28.1, C30.1, C31.1, C32.1, C33.1, C34.1, C35.1, C36.1, C37.1, C38.1, C40.1, C41.1, C42.1, C43.1, C44.1, C45.1, C46.1, C47.1, C48.1, C50.1, C51.1, C52.1, C53.1, C54.1, C55.1, C56.1, C57.1, C58.1, C60.1, C61.1, C62.1, C63.1, M7.2, M7.3, M8.2, M8.3, M9.2, M9.3, M51.1, M51.2, M51.3, M51.4, TP1.1, TP2.1
