Board-Folk/Einstein-TC-01/Kicad/einstein_psgkeyboard.kicad_sch

## KiCad design Kicad/einstein_psgkeyboard.kicad_sch (2025-11-02)

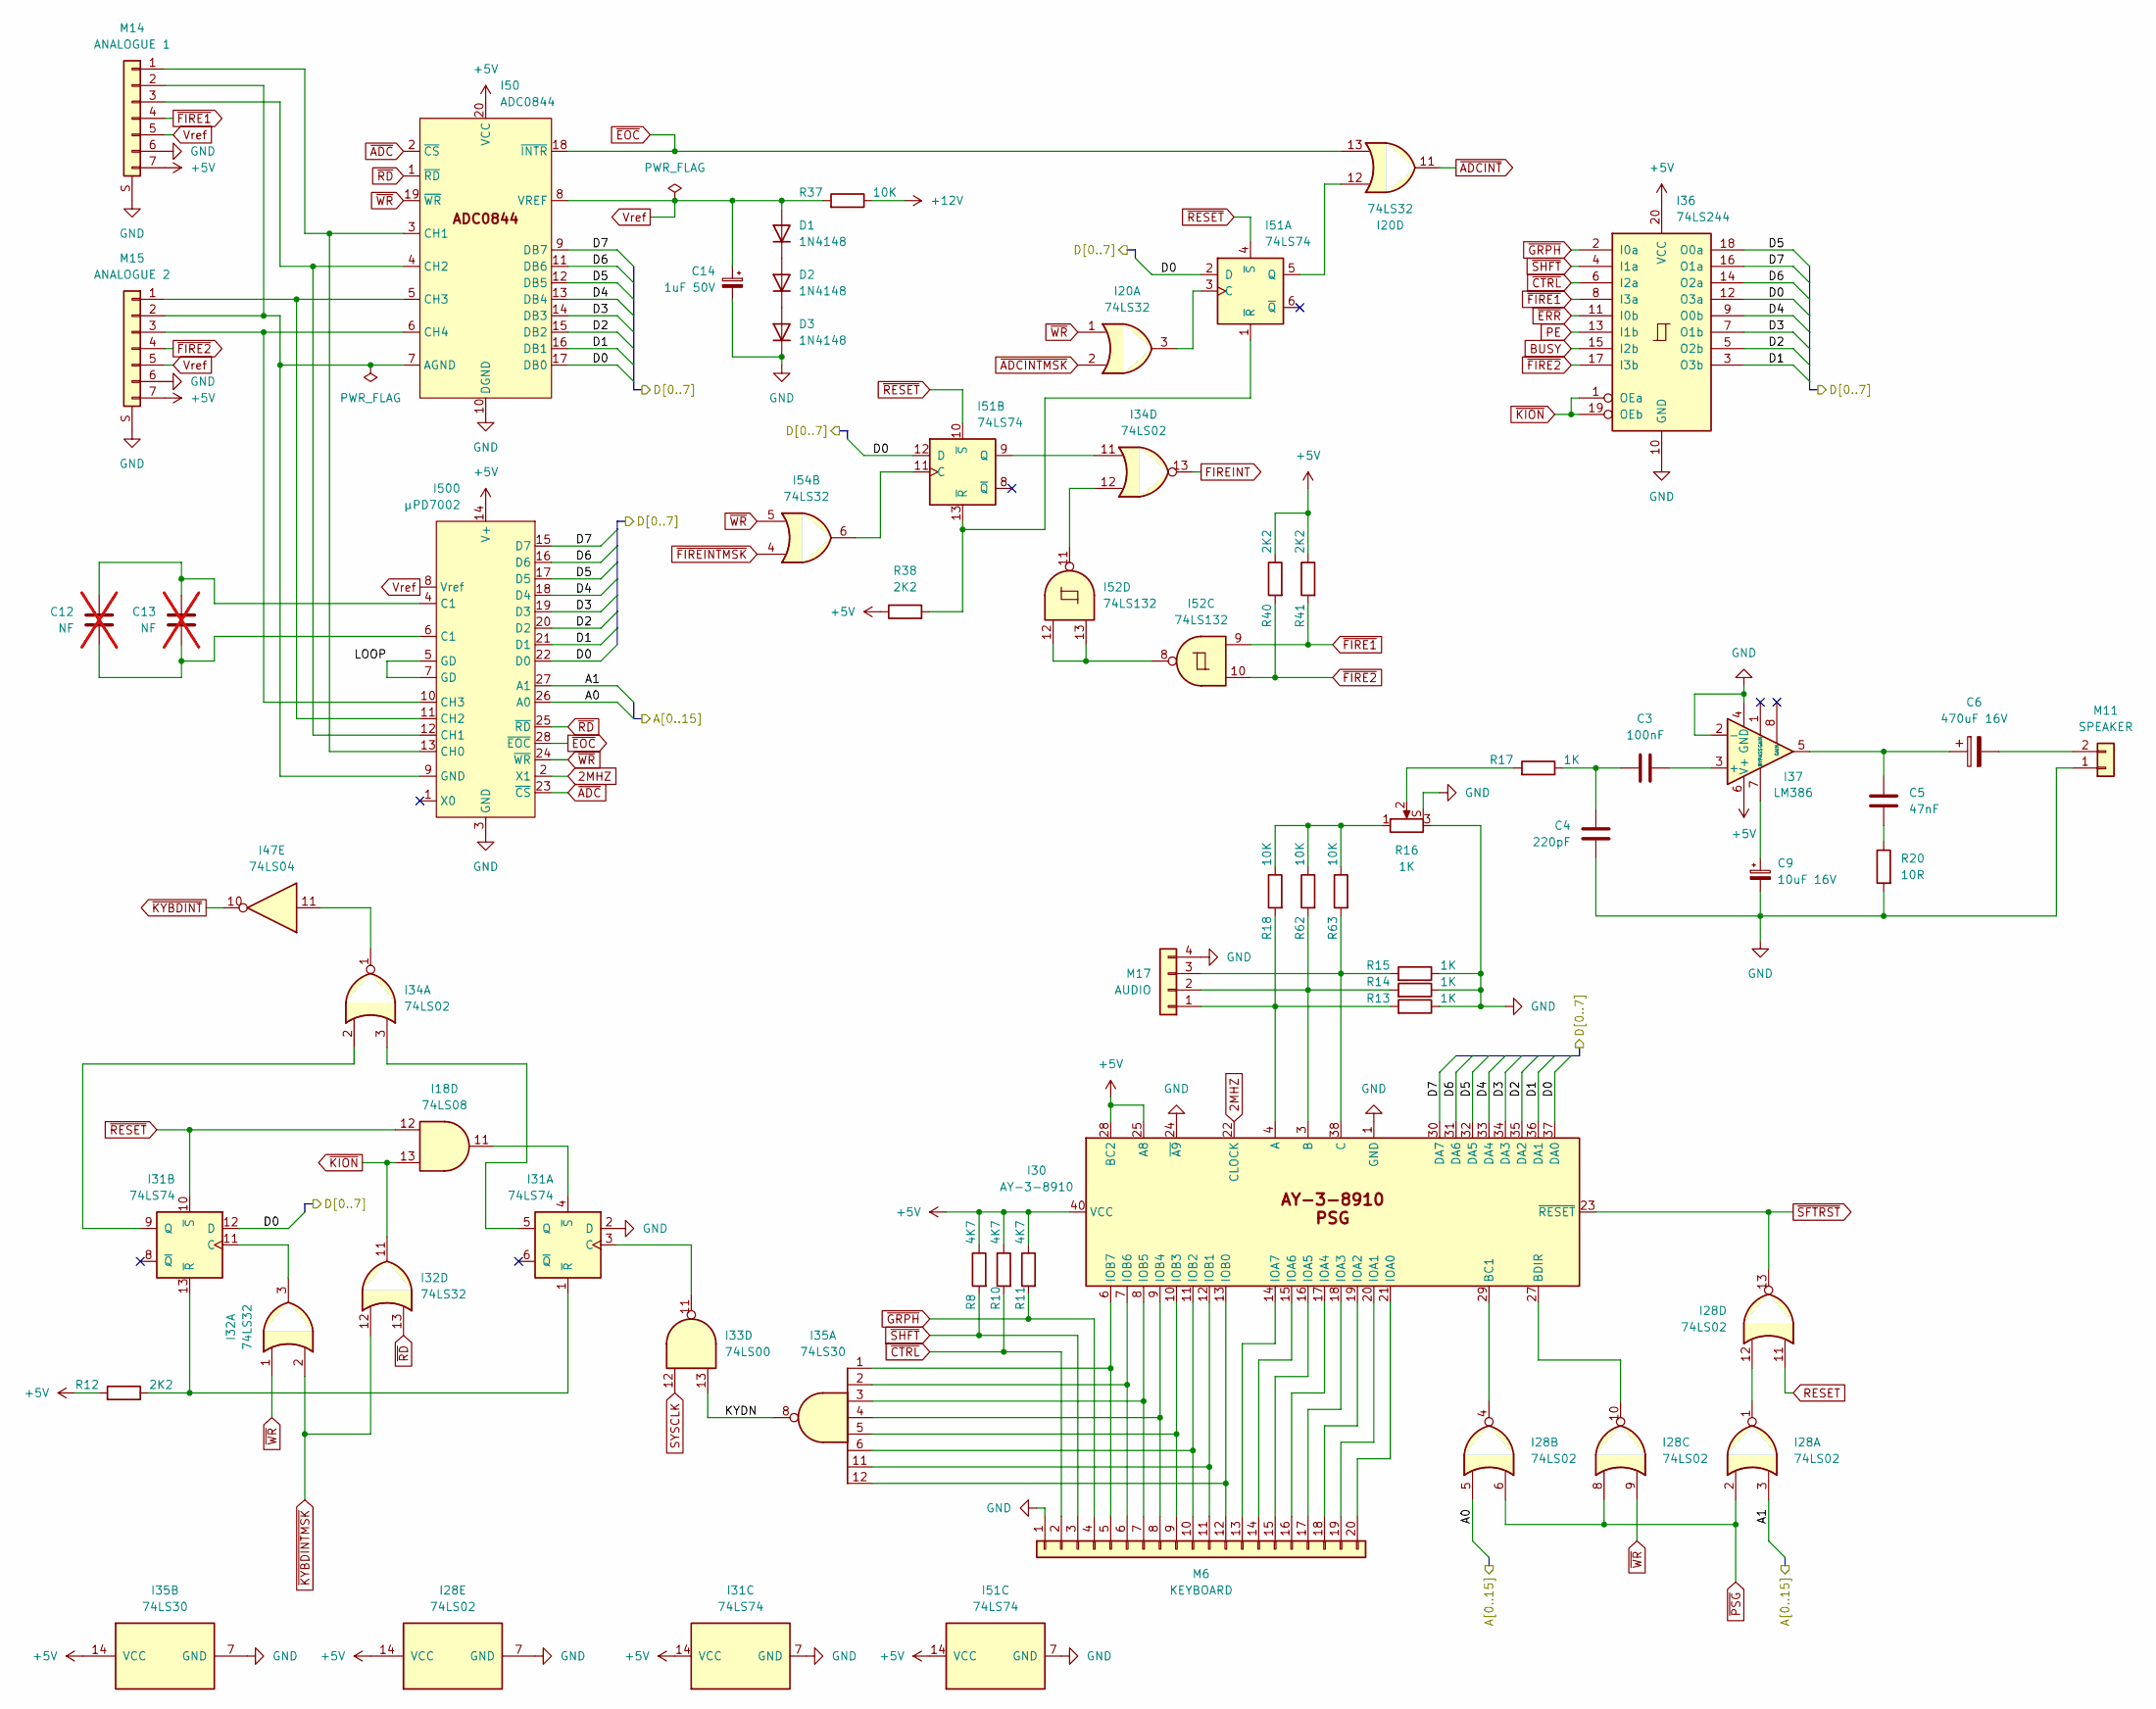
[picture p47: schematic einstein_psgkeyboard.kicad_sch]

Parts:
C3: 100nF; C_Disc_10.16mm
C4: 220pF; C_Disc_12.7mm
C5: 47nF; C_Disc_10.16mm
C6: 470uF 16V; Elec_5.08mm - Big Box
C9: 10uF 16V; Elec_5.08mm - Box
C12, C13: NF; C_Disc_5.08mm; not fitted
C14: 1uF 50V; Elec_5.08mm - Box
D1, D2, D3: 1N4148; Diode 10.16mm
I18: 74LS08; DIP-14_W7.62mm
I20, I32, I54: 74LS32; DIP-14_W7.62mm
I28, I34: 74LS02; DIP-14_W7.62mm
I30: AY-3-8910; DIP-40_W15.24mm
I31, I51: 74LS74; DIP-14_W7.62mm
I33: 74LS00; DIP-14_W7.62mm
I35: 74LS30; DIP-14_W7.62mm
I36: 74LS244; DIP-20_W7.62mm
I37: LM386; DIP-8_W7.62mm
I47: 74LS04; DIP-14_W7.62mm
I50: ADC0844; DIP-20_W7.62mm
I52: 74LS132; DIP-14_W7.62mm
I500: µPD7002; DIP-28_W15.24mm
M6: KEYBOARD; Keyboard
M11: SPEAKER; M11 PinHeader_1x02_P2.54mm
M14: ANALOGUE 1; DIN7_3WAYS
M15: ANALOGUE 2; DIN7_3WAYS
M17: AUDIO; M17 PinHeader_1x04_P2.54mm
R8, R10, R11: 4K7; Resistor 12.70mm
R12, R38, R40, R41: 2K2; Resistor 12.70mm
R13, R14, R15, R17: 1K; Resistor 12.70mm
R16: 1K; Volume
R18, R37, R62, R63: 10K; Resistor 12.70mm
R20: 10R; Resistor 12.70mm

Connections:
2MHZ: I30.22 (CLOCK), I500.2 (X1)
+5V: I28.14 (VCC), I30.25 (A8), I30.28 (BC2), I30.40 (VCC), I31.14 (VCC), I35.14 (VCC), I36.20 (VCC), I37.6 (V+), I50.20 (VCC), I51.14 (VCC), I500.14 (V+), M14.7, M15.7, R8.1, R10.1, R11.1, R12.2, R38.1, R40.1, R41.1
+12V: R37.1
A0: I28.5, I500.26 (A0)
A1: I28.3, I500.27 (A1)
BUSY: I36.15 (I2b)
D0: I30.37 (DA0), I31.12 (D), I36.12 (O3a), I50.17 (DB0), I51.2 (D), I51.12 (D), I500.22 (D0)
D1: I30.36 (DA1), I36.3 (O3b), I50.16 (DB1), I500.21 (D1)
D2: I30.35 (DA2), I36.5 (O2b), I50.15 (DB2), I500.20 (D2)
D3: I30.34 (DA3), I36.7 (O1b), I50.14 (DB3), I500.19 (D3)
D4: I30.33 (DA4), I36.9 (O0b), I50.13 (DB4), I500.18 (D4)
D5: I30.32 (DA5), I36.18 (O0a), I50.12 (DB5), I500.17 (D5)
D6: I30.31 (DA6), I36.14 (O2a), I50.11 (DB6), I500.16 (D6)
D7: I30.30 (DA7), I36.16 (O1a), I50.9 (DB7), I500.15 (D7)
FIREINT: I34.13
GND: C4.2, C9.2, C14.2, D3.1 (K), I28.7 (GND), I30.1 (GND), I30.24 (~A9), I31.2 (D), I31.7 (GND), I35.7 (GND), I36.10 (GND), I37.2 (-), I37.4 (GND), I50.10 (DGND), I51.7 (GND), I500.3 (GND), M6.1, M11.1, M14.6, M14.S (Shield), M15.6, M15.S (Shield), M17.4, R13.1, R14.1, R15.1, R16.3, R16.S, R20.2
KYDN: I33.13, I35.8
LOOP: I500.5 (GD), I500.7 (GD)
unnamed: C3.1, I37.3 (+)
unnamed: C3.2, C4.1, R17.1
unnamed: C5.1, C6.1, I37.5
unnamed: C5.2, R20.1
unnamed: C6.2, M11.2
unnamed: C9.1, I37.7 (BYPASS)
unnamed: C12.1, C13.1, I500.4 (C1)
unnamed: C12.2, C13.2, I500.6 (C1)
unnamed: D1.1 (K), D2.2 (A)
unnamed: D2.1 (K), D3.2 (A)
unnamed: I18.11, I31.4 (~S)
unnamed: I20.3, I51.3 (C)
unnamed: I20.12, I51.5 (Q)
unnamed: I28.1, I28.12
unnamed: I28.4, I30.29 (BC1)
unnamed: I28.10, I30.27 (BDIR)
unnamed: I30.3 (B), M17.2, R14.2, R62.2
unnamed: I30.4 (A), M17.1, R13.2, R18.2
unnamed: I30.6 (IOB7), I35.1, M6.5
unnamed: I30.7 (IOB6), I35.2, M6.6
unnamed: I30.8 (IOB5), I35.3, M6.7
unnamed: I30.9 (IOB4), I35.4, M6.8
unnamed: I30.10 (IOB3), I35.5, M6.9
unnamed: I30.11 (IOB2), I35.6, M6.10
unnamed: I30.12 (IOB1), I35.11, M6.11
unnamed: I30.13 (IOB0), I35.12, M6.12
unnamed: I30.14 (IOA7), M6.13
unnamed: I30.15 (IOA6), M6.14
unnamed: I30.16 (IOA5), M6.15
unnamed: I30.17 (IOA4), M6.16
unnamed: I30.18 (IOA3), M6.17
unnamed: I30.19 (IOA2), M6.18
unnamed: I30.20 (IOA1), M6.19
unnamed: I30.21 (IOA0), M6.20
unnamed: I30.38 (C), M17.3, R15.2, R63.2
unnamed: I31.1 (~R), I31.13 (~R), R12.1
unnamed: I31.3 (C), I33.11
unnamed: I31.5 (Q), I34.3
unnamed: I31.9 (Q), I34.2
unnamed: I31.11 (C), I32.3
unnamed: I34.1, I47.11
unnamed: I34.11, I51.9 (Q)
unnamed: I34.12, I52.11
unnamed: I50.3 (CH1), I500.13 (CH0), M14.1
unnamed: I50.4 (CH2), I500.12 (CH1), M14.3
unnamed: I50.5 (CH3), I500.11 (CH2), M15.1
unnamed: I50.6 (CH4), I500.10 (CH3), M15.3
unnamed: I50.7 (AGND), I500.9 (GND), M14.2, M15.2
unnamed: I51.1 (~R), I51.13 (~R), R38.2
unnamed: I51.11 (C), I54.6
unnamed: I52.8, I52.12, I52.13
unnamed: R16.1, R18.1, R62.1, R63.1
unnamed: R16.2, R17.2
PE: I36.13 (I1b)
RESET: I28.11
SYSCLK: I33.12
Vref: C14.1, D1.2 (A), I50.8 (VREF), I500.8 (Vref), M14.5, M15.5, R37.2
~ADCINTMSK: I20.2
~ADCINT: I20.11
~ADC: I50.2 (~CS), I500.23 (~CS)
~CTRL: I36.6 (I2a), M6.2, R10.2
~EOC: I20.13, I50.18 (~INTR), I500.28 (~EOC)
~ERR: I36.11 (I0b)
~FIRE1: I36.8 (I3a), I52.9, M14.4, R41.2
~FIRE2: I36.17 (I3b), I52.10, M15.4, R40.2
~FIREINTMSK: I54.4
~GRPH: I36.2 (I0a), M6.4, R11.2
~KION: I18.13, I32.11, I36.1 (OEa), I36.19 (OEb)
~KYBDINTMSK: I32.2, I32.12
~KYBDINT: I47.10
~PSG: I28.2, I28.6, I28.8
~RD: I32.13, I50.1 (~RD), I500.25 (~RD)
~RESET: I18.12, I31.10 (~S), I51.4 (~S), I51.10 (~S)
~SFTRST: I28.13, I30.23 (~RESET)
~SHFT: I36.4 (I1a), M6.3, R8.2
~WR: I20.1, I28.9, I32.1, I50.19 (~WR), I54.5, I500.24 (~WR)
