Board-Folk/Einstein-TC-01/Kicad/einstein_rgb.kicad_sch

## KiCad design Kicad/einstein_rgb.kicad_sch (2026-03-14)

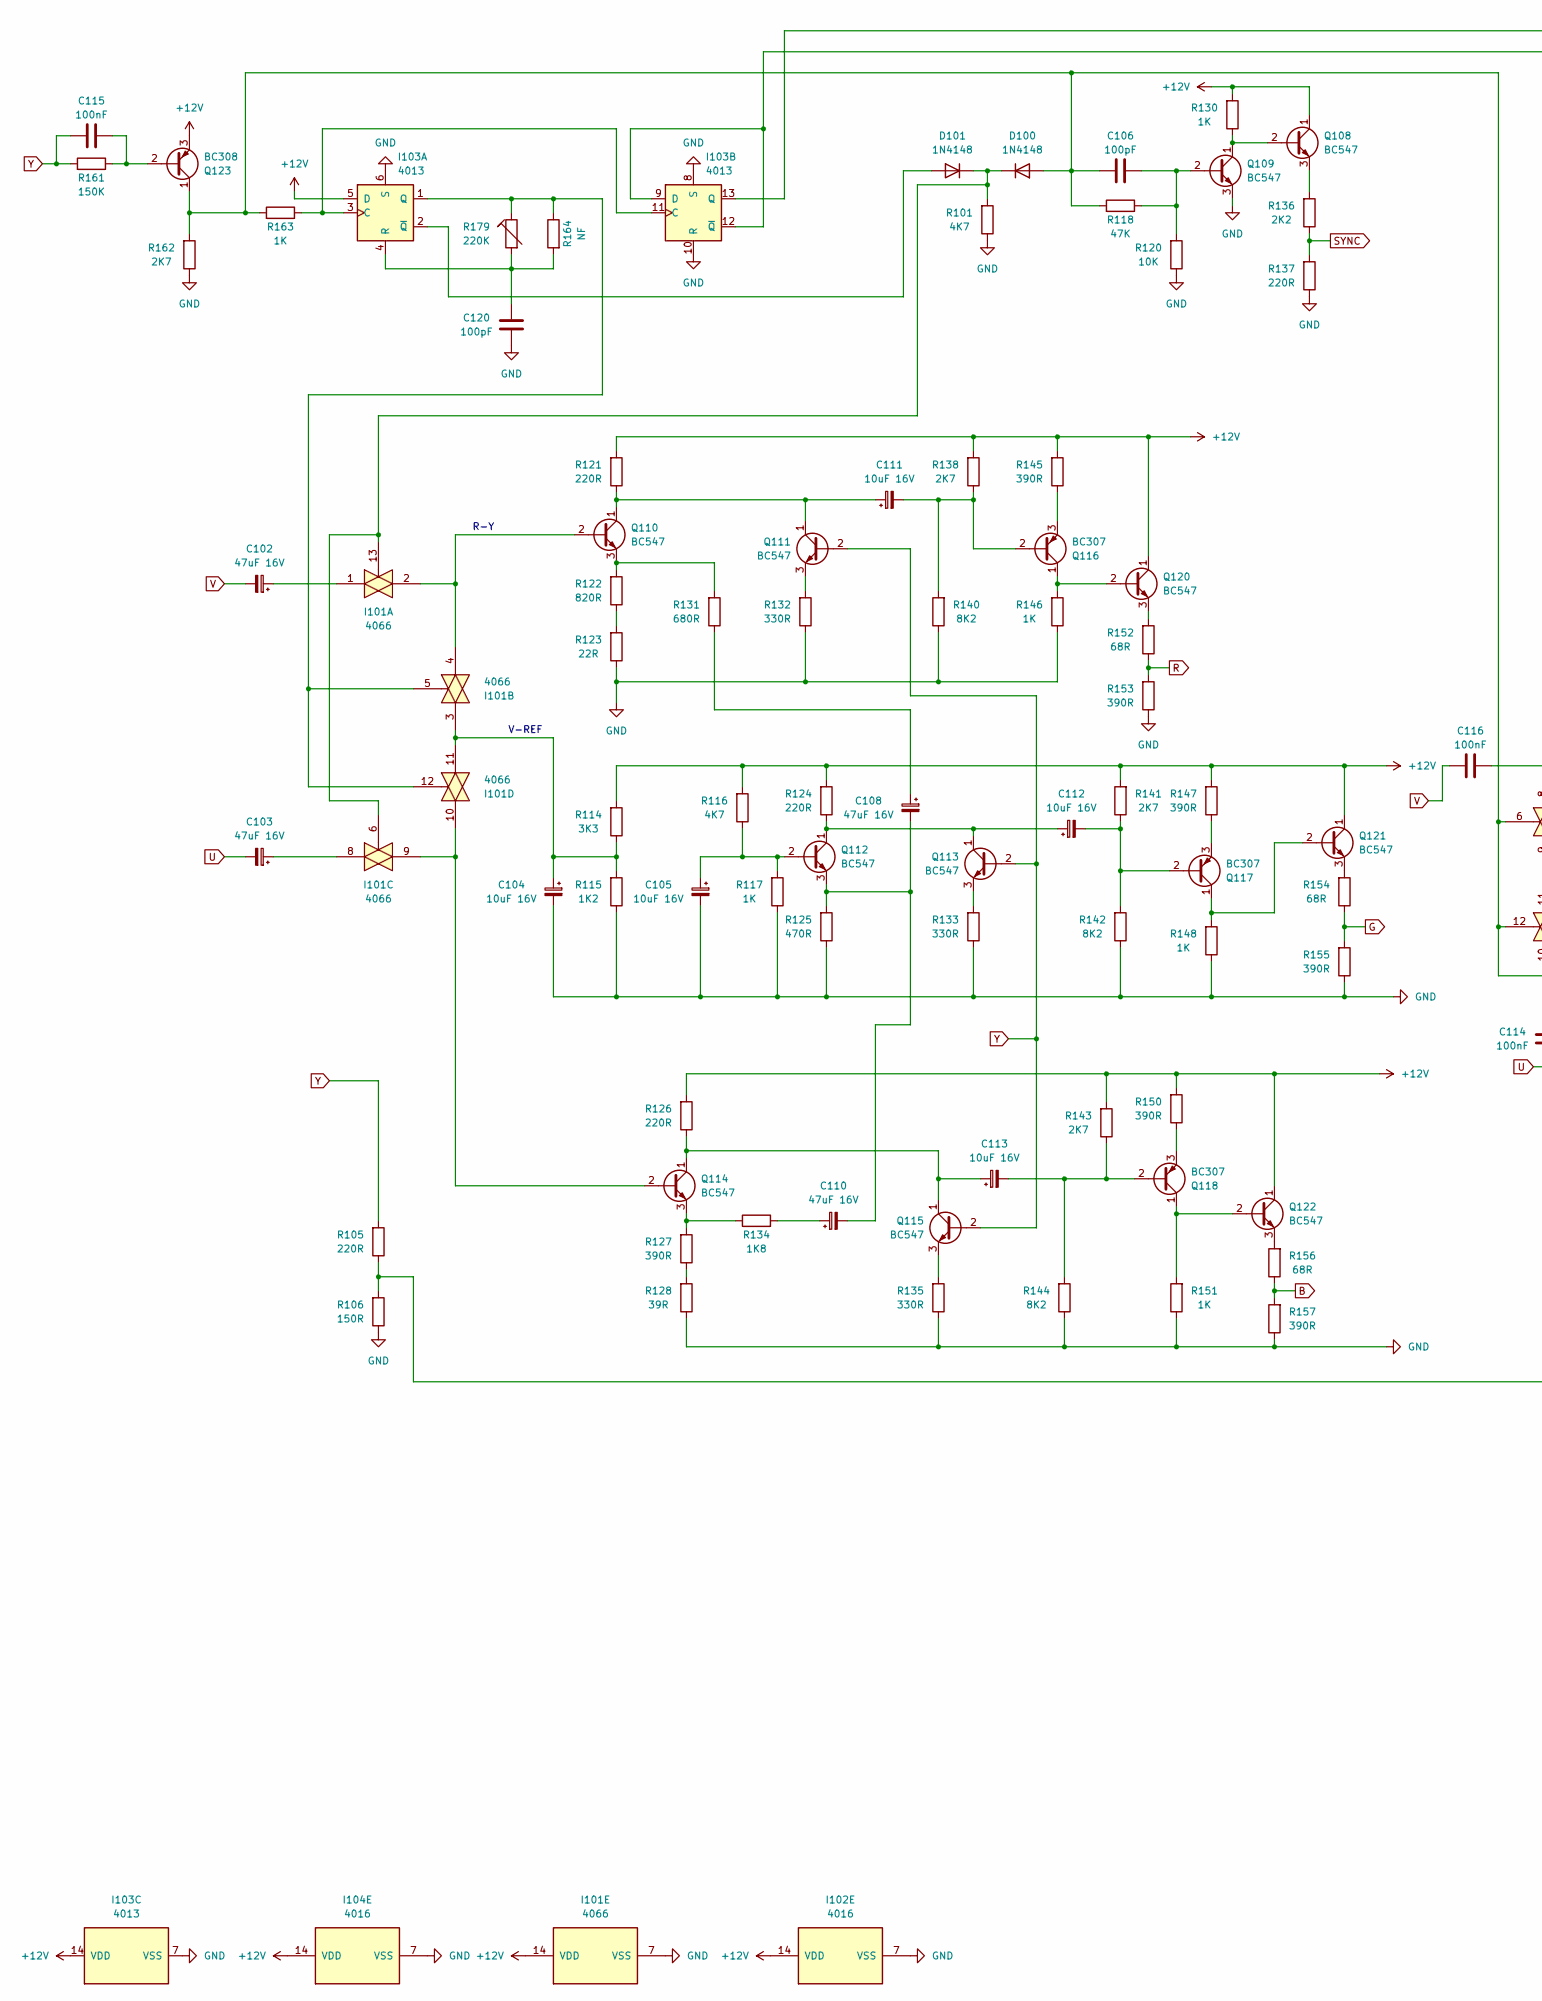
[picture p48: schematic einstein_rgb.kicad_sch, part in row 1, column 1]

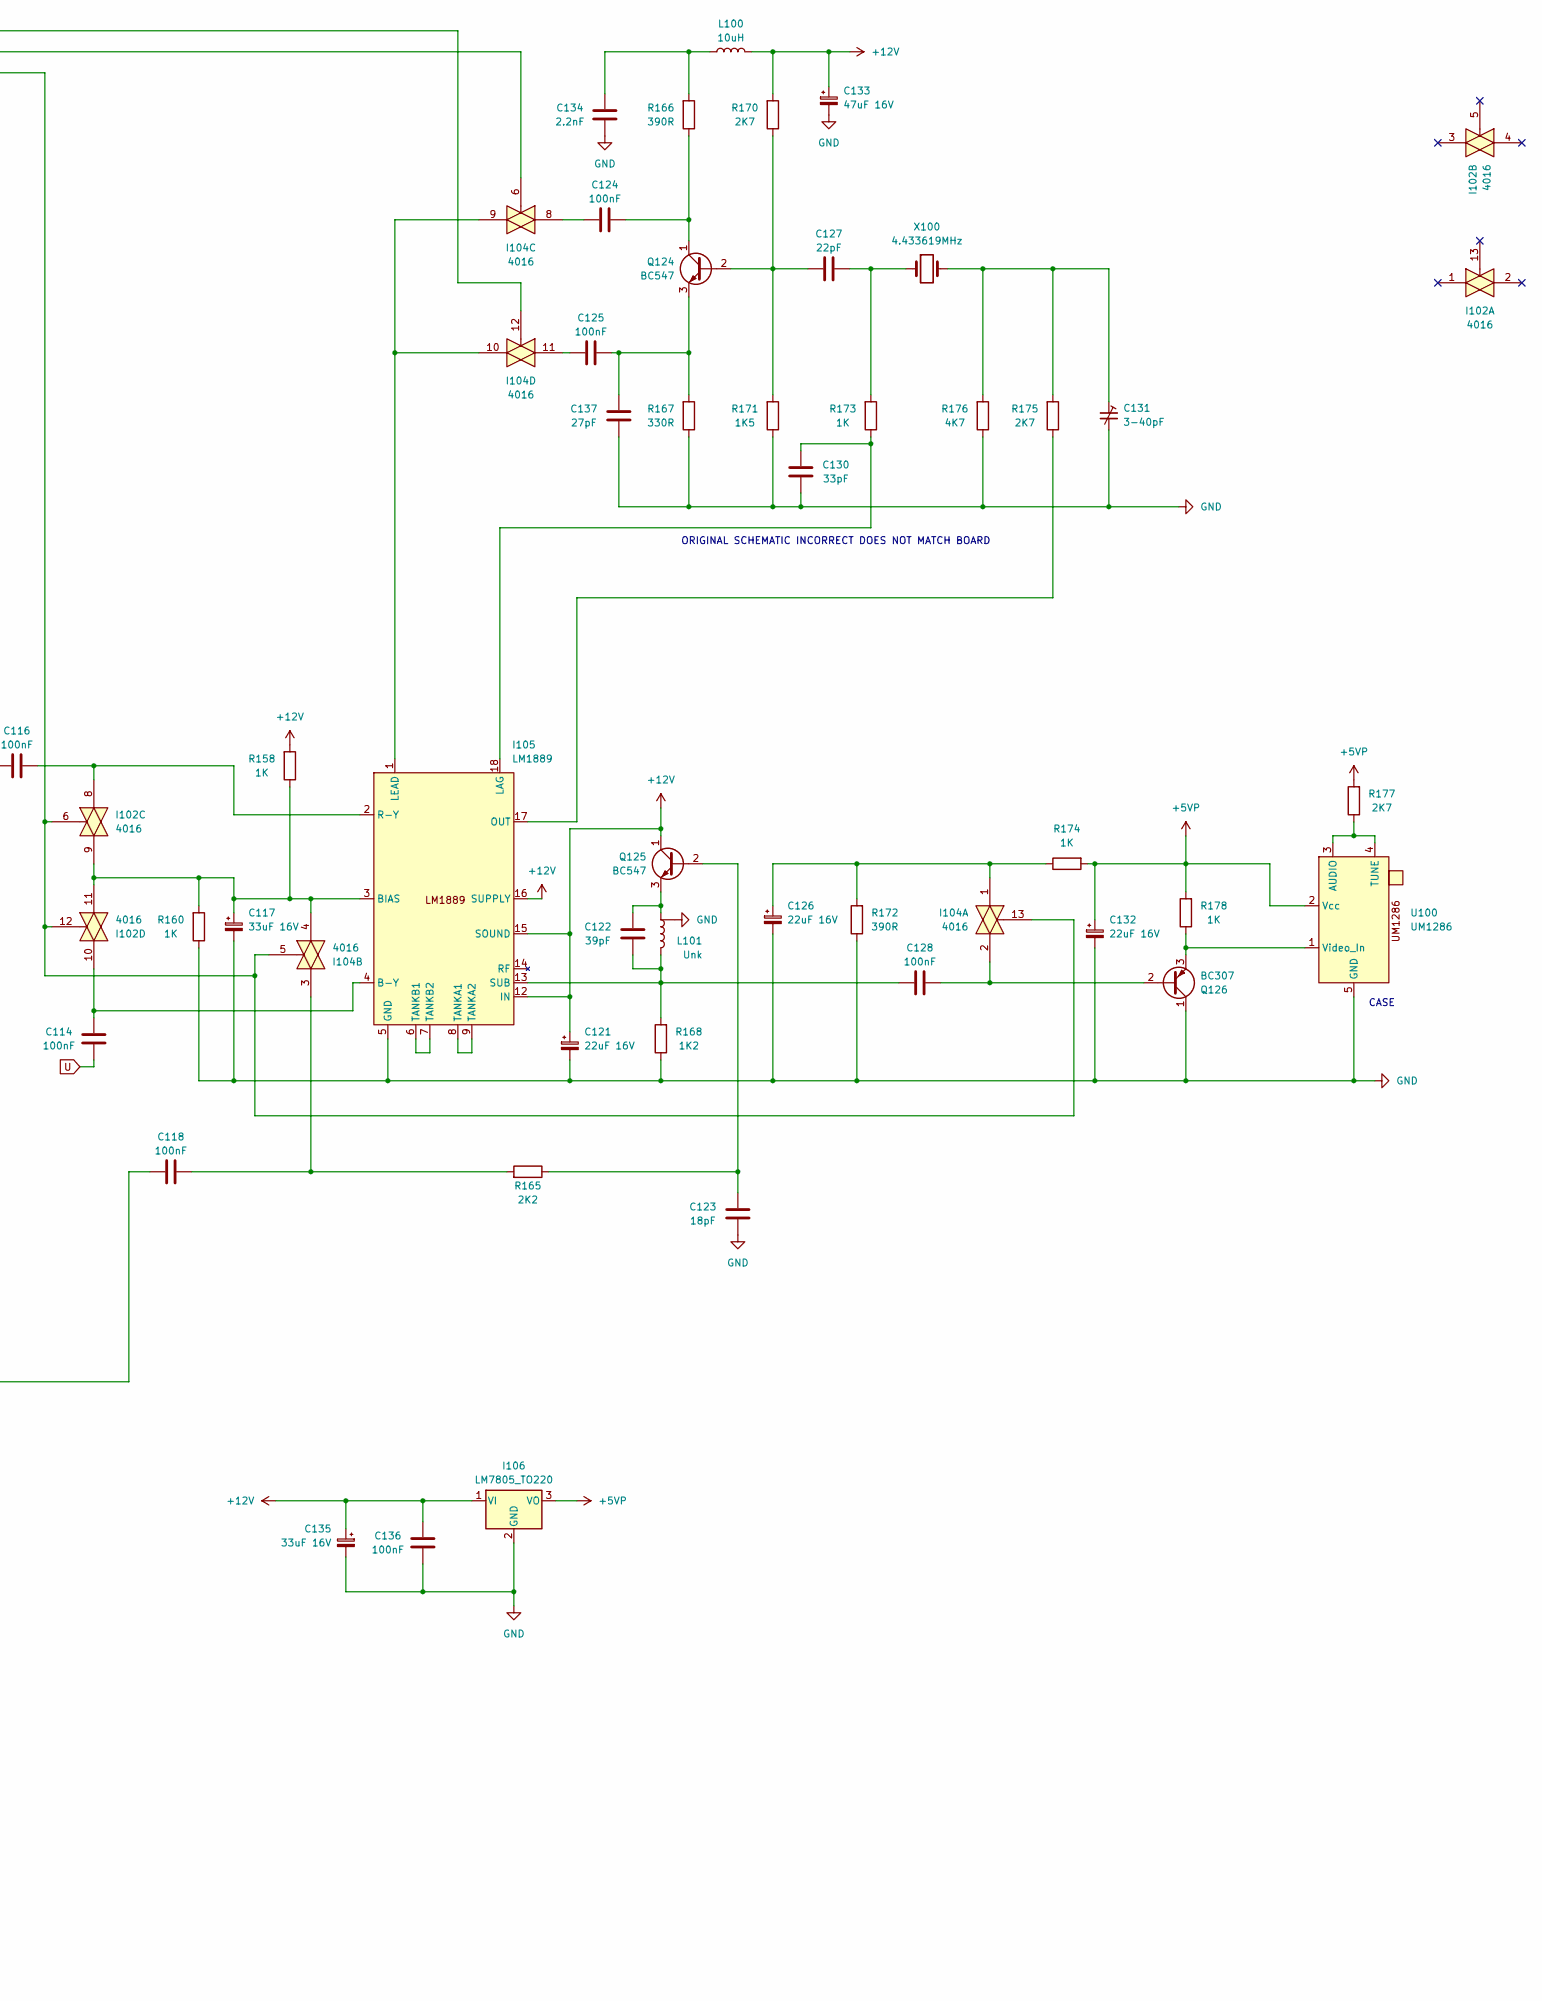
[picture p49: schematic einstein_rgb.kicad_sch, part in row 1, column 2]

Parts:
C102, C103, C108, C110, C133: 47uF 16V; Elec_5.08mm - Box
C104, C105, C111, C112, C113: 10uF 16V; Elec_5.08mm - Box
C106, C120: 100pF; C_Disc_12.7mm
C114, C115, C116, C118, C124, C125, C128, C136: 100nF; C_Disc_10.16mm
C117, C135: 33uF 16V; Elec_5.08mm - Box
C121, C126, C132: 22uF 16V; Elec_5.08mm - Box
C122: 39pF; C_Disc_2.54mm
C123: 18pF; C_Disc_2.54mm
C127: 22pF; C_Disc_2.54mm
C130: 33pF; C_Disc_2.54mm
C131: 3-40pF; Trimmer
C134: 2.2nF; C_Disc_5.08mm
C137: 27pF; C_Disc_5.08mm
D100, D101: 1N4148; Diode 10.16mm
I101: 4066; DIP-14_W7.62mm
I102, I104: 4016; DIP-14_W7.62mm
I103: 4013; DIP-14_W7.62mm
I105: LM1889; DIP-18_W7.62mm
I106: LM7805_TO220; Regulator TO-220-3
L100: 10uH; Resistor 12.70mm
L101: Unk; L Adjustable
Q108, Q109, Q110, Q111, Q112, Q113, Q114, Q115, Q120, Q121, Q122, Q124, Q125: BC547; Transistor - Box 1 (Leg Rear)
Q116, Q117, Q118, Q126: BC307; Transistor - Box 1 (Leg Rear)
Q123: BC308; Transistor - Box 1 (Leg Rear)
R101, R116, R176: 4K7; Resistor 12.70mm
R105, R121, R124, R126, R137: 220R; Resistor 12.70mm
R106: 150R; Resistor 12.70mm
R114: 3K3; Resistor 12.70mm
R115, R168: 1K2; Resistor 12.70mm
R117, R130, R146, R148, R151, R158, R160, R163, R173, R174, R178: 1K; Resistor 12.70mm
R118: 47K; Resistor 12.70mm
R120: 10K; Resistor 12.70mm
R122: 820R; Resistor 12.70mm
R123: 22R; Resistor 12.70mm
R125: 470R; Resistor 12.70mm
R127, R145, R147, R150, R153, R155, R157, R166, R172: 390R; Resistor 12.70mm
R128: 39R; Resistor 12.70mm
R131: 680R; Resistor 12.70mm
R132, R133, R135, R167: 330R; Resistor 12.70mm
R134: 1K8; Resistor 12.70mm
R136, R165: 2K2; Resistor 12.70mm
R138, R141, R143, R162, R170, R175, R177: 2K7; Resistor 12.70mm
R140, R142, R144: 8K2; Resistor 12.70mm
R152, R154, R156: 68R; Resistor 12.70mm
R161: 150K; Resistor 12.70mm
R164: NF; Resistor 12.70mm
R171: 1K5; Resistor 12.70mm
R179: 220K; Pot
U100: UM1286
X100: 4.433619MHz; Crystal

Connections:
+5VP: C132.1, I106.3 (VO), R174.2, R177.2, R178.2, U100.2 (Vcc)
+12V: C121.1, C133.1, C135.1, C136.2, I101.14 (VDD), I102.14 (VDD), I103.5 (D), I103.14 (VDD), I104.14 (VDD), I105.12 (IN), I105.15 (SOUND), I105.16 (SUPPLY), I106.1 (VI), L100.2, Q108.1 (C), Q120.1 (C), Q121.1 (C), Q122.1 (C), Q123.3 (E), Q125.1 (C), R114.2, R116.2, R121.2, R124.2, R126.2, R130.2, R138.2, R141.2, R143.2, R145.2, R147.2, R150.2, R158.2, R170.2
B: R156.1, R157.2
G: R154.1, R155.2
GND: C104.2, C105.2, C117.2, C120.1, C121.2, C123.1, C126.2, C130.1, C131.2, C132.2, C133.2, C134.1, C135.2, C136.1, C137.1, I101.7 (VSS), I102.7 (VSS), I103.6 (S), I103.7 (VSS), I103.8 (S), I103.10 (R), I104.7 (VSS), I105.5 (GND), I106.2 (GND), L101.S, Q109.3 (E), Q126.1 (C), R101.1, R106.1, R115.1, R117.1, R120.1, R123.1, R125.1, R128.1, R132.1, R133.1, R135.1, R137.1, R140.1, R142.1, R144.1, R146.1, R148.1, R151.1, R153.1, R155.1, R157.1, R160.1, R162.1, R167.1, R168.1, R171.1, R172.1, R176.1, U100.5 (GND)
unnamed: C102.1, I101.1
unnamed: C103.1, I101.8
unnamed: C104.1, I101.3, I101.11, R114.1, R115.2
unnamed: C105.1, Q112.2 (B), R116.1, R117.2
unnamed: C106.1, D100.2 (A), I102.6, I102.12, I104.5, I104.13, Q123.1 (C), R118.2, R162.2, R163.2
unnamed: C106.2, Q109.2 (B), R118.1, R120.2
unnamed: C108.1, R131.1
unnamed: C108.2, C110.2, Q112.3 (E), R125.2
unnamed: C110.1, R134.2
unnamed: C111.1, Q110.1 (C), Q111.1 (C), R121.1
unnamed: C111.2, Q116.2 (B), R138.1, R140.2
unnamed: C112.1, Q112.1 (C), Q113.1 (C), R124.1
unnamed: C112.2, Q117.2 (B), R141.1, R142.2
unnamed: C113.1, Q114.1 (C), Q115.1 (C), R126.1
unnamed: C113.2, Q118.2 (B), R143.1, R144.2
unnamed: C114.2, I102.10, I105.4 (B-Y)
unnamed: C115.2, Q123.2 (B), R161.1
unnamed: C116.2, I102.8, I105.2 (R-Y)
unnamed: C117.1, I102.9, I102.11, I104.4, I105.3 (BIAS), R158.1, R160.2
unnamed: C118.1, R105.1, R106.2
unnamed: C118.2, I104.3, R165.2
unnamed: C120.2, I103.4 (R), R164.2, R179.2
unnamed: C122.1, C128.1, I105.13 (SUB), L101.1, R168.2
unnamed: C122.2, L101.2, Q125.3 (E)
unnamed: C123.2, Q125.2 (B), R165.1
unnamed: C124.1, I104.8
unnamed: C124.2, Q124.1 (C), R166.1
unnamed: C125.1, I104.11
unnamed: C125.2, C137.2, Q124.3 (E), R167.2
unnamed: C126.1, I104.1, R172.2, R174.1
unnamed: C127.1, Q124.2 (B), R170.1, R171.2
unnamed: C127.2, R173.2, X100.1
unnamed: C128.2, I104.2, Q126.2 (B)
unnamed: C130.2, I105.18 (LAG), R173.1
unnamed: C131.1, R175.2, R176.2, X100.2
unnamed: C134.2, L100.1, R166.2
unnamed: D100.1 (K), D101.1 (K), I101.6, I101.13, R101.2
unnamed: D101.2 (A), I103.2 (~Q)
unnamed: I101.2, I101.4, Q110.2 (B)
unnamed: I101.9, I101.10, Q114.2 (B)
unnamed: I101.5, I101.12, I103.1 (Q), R164.1, R179.1
unnamed: I103.3 (C), I103.11 (C), R163.1
unnamed: I103.9 (D), I103.12 (~Q), I104.6
unnamed: I103.13 (Q), I104.12
unnamed: I104.9, I104.10, I105.1 (LEAD)
unnamed: I105.6 (TANKB1), I105.7 (TANKB2)
unnamed: I105.8 (TANKA1), I105.9 (TANKA2)
unnamed: I105.17 (OUT), R175.1
unnamed: Q108.2 (B), Q109.1 (C), R130.1
unnamed: Q108.3 (E), R136.2
unnamed: Q110.3 (E), R122.2, R131.2
unnamed: Q111.3 (E), R132.2
unnamed: Q113.3 (E), R133.2
unnamed: Q114.3 (E), R127.2, R134.1
unnamed: Q115.3 (E), R135.2
unnamed: Q116.1 (C), Q120.2 (B), R146.2
unnamed: Q116.3 (E), R145.1
unnamed: Q117.1 (C), Q121.2 (B), R148.2
unnamed: Q117.3 (E), R147.1
unnamed: Q118.1 (C), Q122.2 (B), R151.2
unnamed: Q118.3 (E), R150.1
unnamed: Q120.3 (E), R152.2
unnamed: Q121.3 (E), R154.2
unnamed: Q122.3 (E), R156.2
unnamed: Q126.3 (E), R178.1, U100.1 (Video_In)
unnamed: R122.1, R123.2
unnamed: R127.1, R128.2
unnamed: R177.1, U100.3 (AUDIO), U100.4 (TUNE)
R: R152.1, R153.2
SYNC: R136.1, R137.2
U: C103.2, C114.1
V: C102.2, C116.1
Y: C115.1, Q111.2 (B), Q113.2 (B), Q115.2 (B), R105.2, R161.2

Notes on the sheet:
CASE
R-Y
ORIGINAL SCHEMATIC INCORRECT DOES NOT MATCH BOARD
V-REF
