Board-Folk/Einstein-TC-01/Kicad/einstein_siopio.kicad_sch

## KiCad design Kicad/einstein_siopio.kicad_sch (2025-11-02)

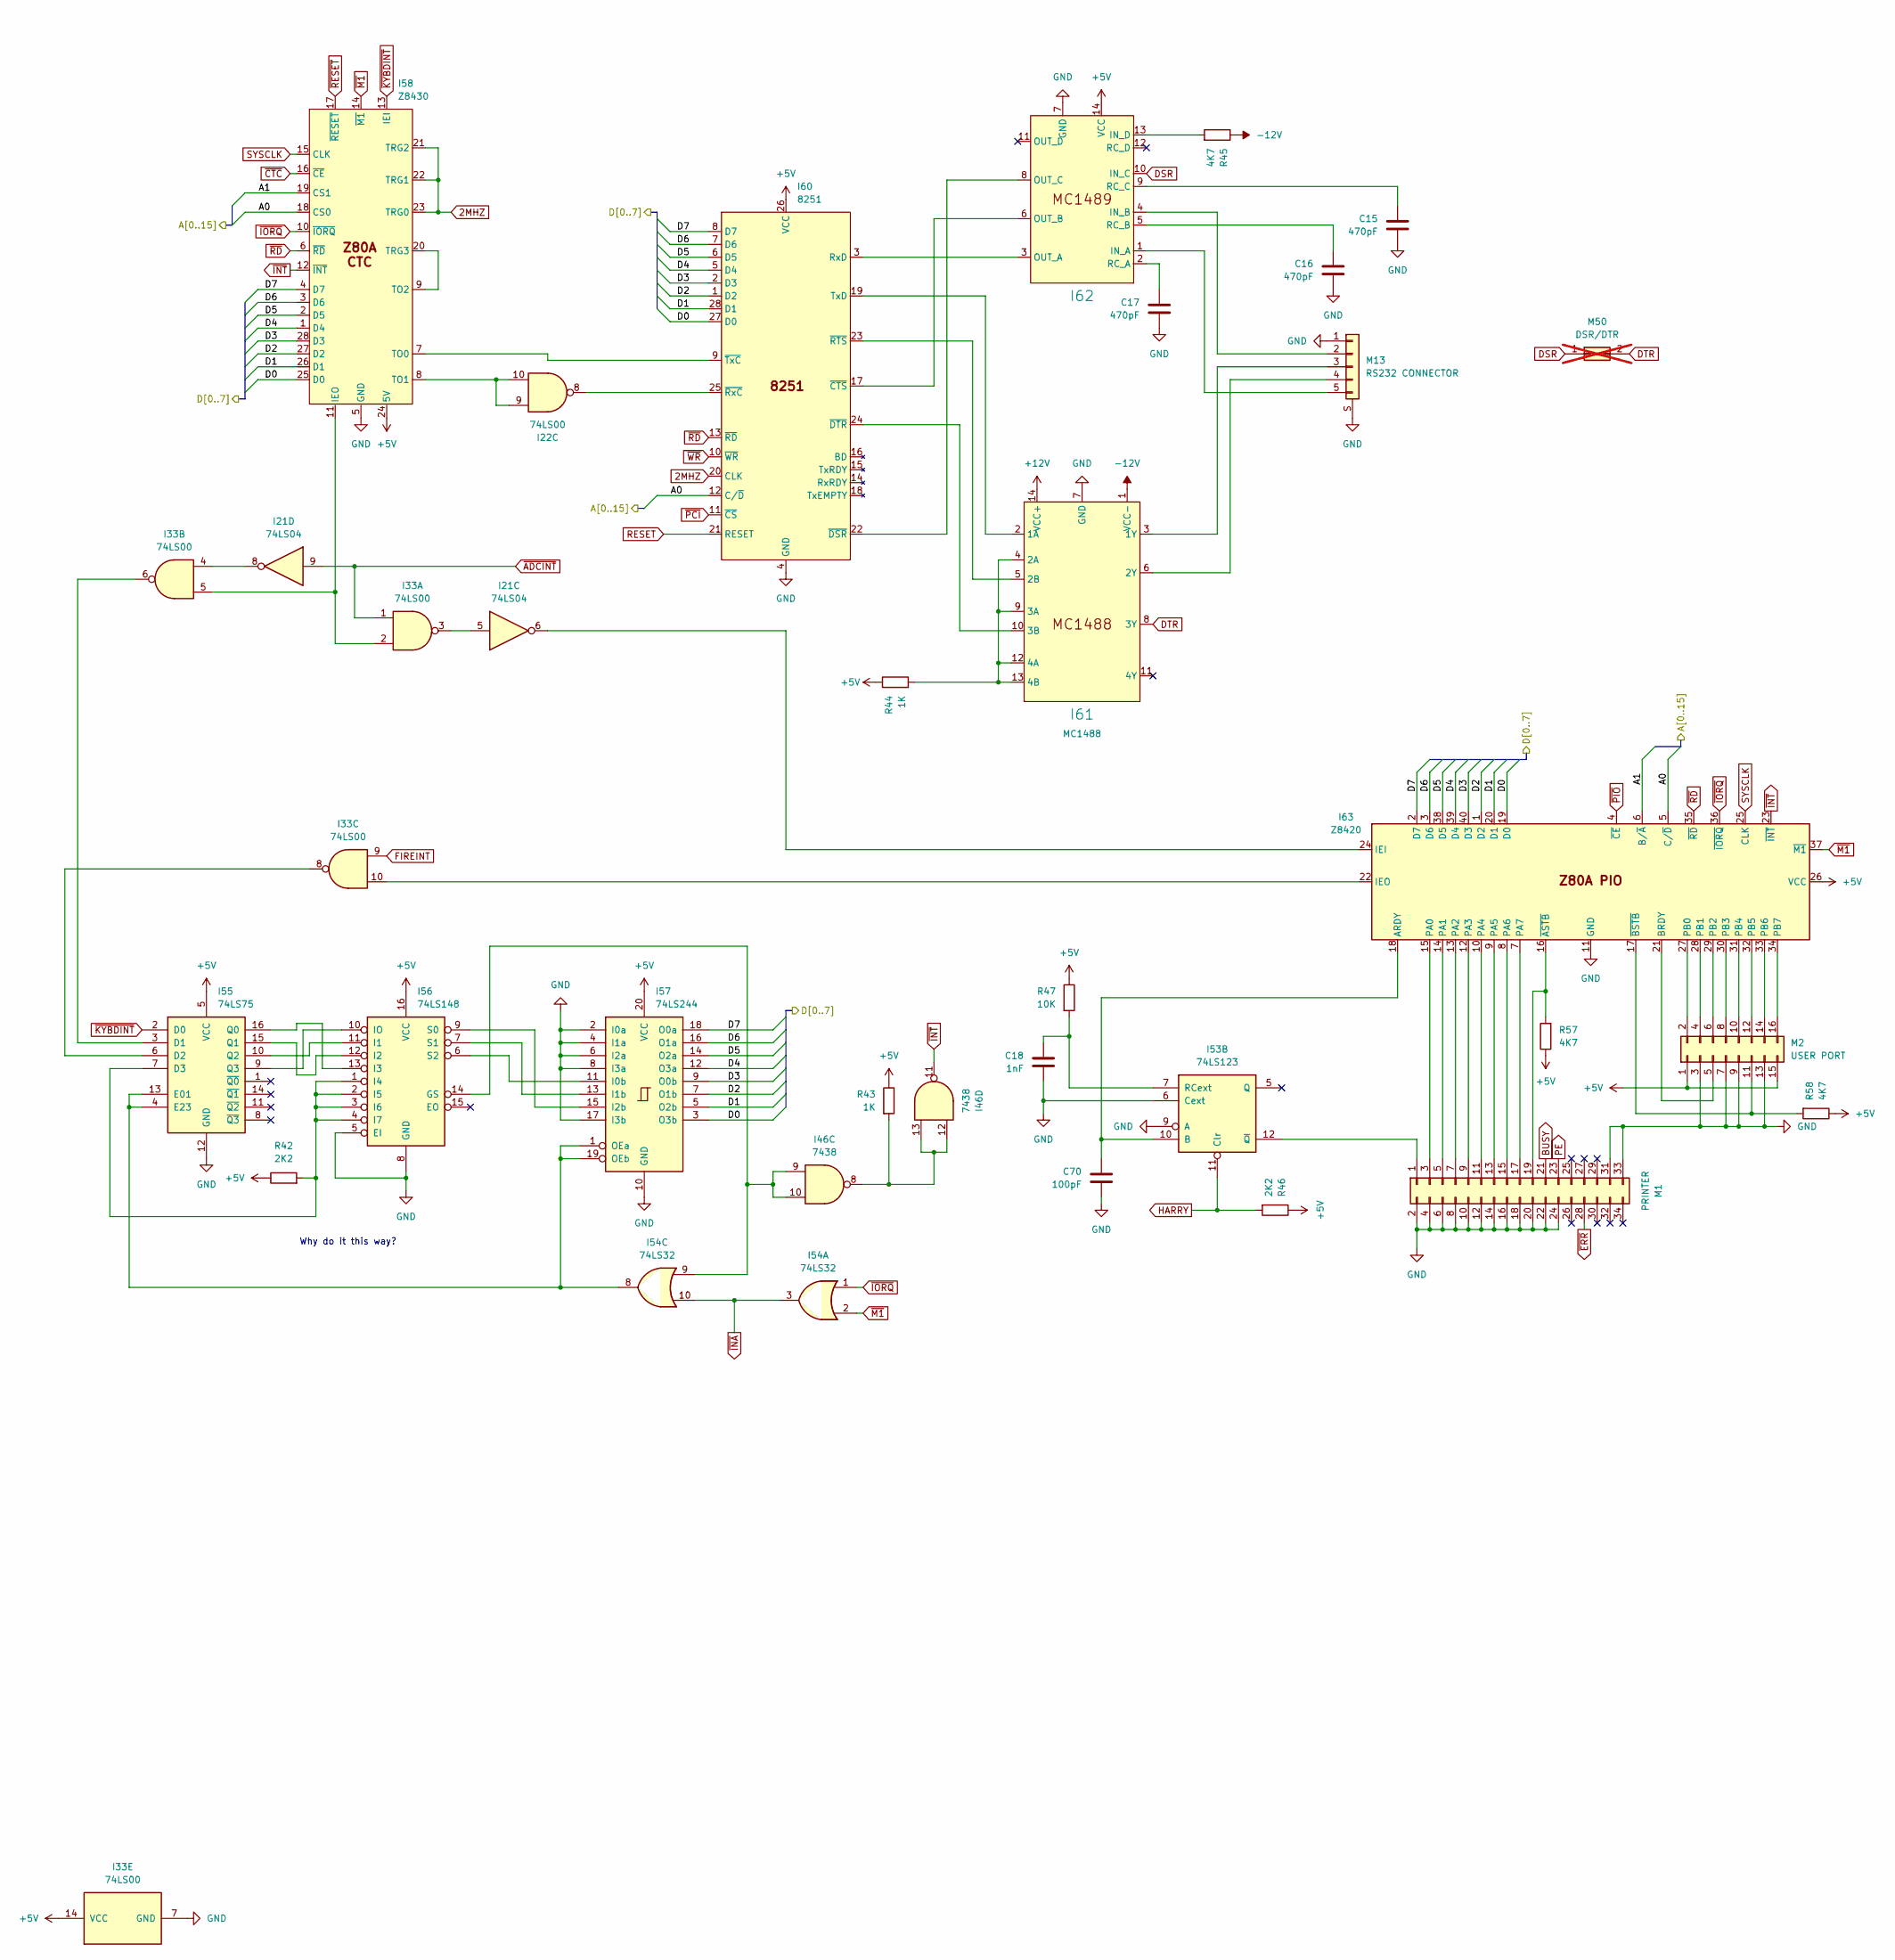
[picture p50: schematic einstein_siopio.kicad_sch]

Parts:
C15, C16, C17: 470pF; C_Disc_12.7mm
C18: 1nF; C_Disc_12.7mm
C70: 100pF; C_Disc_12.7mm
I21: 74LS04; DIP-14_W7.62mm
I22, I33: 74LS00; DIP-14_W7.62mm
I46: 7438; DIP-14_W7.62mm
I53: 74LS123; DIP-16_W7.62mm
I54: 74LS32; DIP-14_W7.62mm
I55: 74LS75; DIP-16_W7.62mm
I56: 74LS148; DIP-16_W7.62mm
I57: 74LS244; DIP-20_W7.62mm
I58: Z8430; DIP-28_W15.24mm
I60: 8251; DIP-28_W15.24mm
I61: MC1488; DIP-14_W7.62mm
I62: MC1489; DIP-14_W7.62mm
I63: Z8420; DIP-40_W15.24mm
M1: PRINTER; PinHeader_2x17_P2.54mm
M2: USER PORT; M2 PinHeader_2x08_P2.54mm
M13: RS232 CONNECTOR; DIN5_DOMINO
M50: DSR/DTR; C_Disc_10.16mm; not fitted
R42, R46: 2K2; Resistor 12.70mm
R43, R44: 1K; Resistor 12.70mm
R45, R57, R58: 4K7; Resistor 12.70mm
R47: 10K; Resistor 12.70mm

Connections:
2MHZ: I58.21 (TRG2), I58.22 (TRG1), I58.23 (TRG0), I60.20 (CLK)
+5V: I33.14 (VCC), I55.5 (VCC), I56.16 (VCC), I57.20 (VCC), I58.24 (5V), I60.26 (VCC), I62.14 (VCC), I63.26 (VCC), M2.1, M2.15, R42.1, R43.1, R44.1, R46.1, R47.1, R57.1, R58.1
+12V: I61.14 (VCC+)
-12V: I61.1 (VCC-), R45.1
A0: I58.18 (CS0), I60.12 (C/~D), I63.5 (C/~D)
A1: I58.19 (CS1), I63.6 (B/~A)
BUSY: M1.21
D0: I57.3 (O3b), I58.25 (D0), I60.27 (D0), I63.19 (D0)
D1: I57.5 (O2b), I58.26 (D1), I60.28 (D1), I63.20 (D1)
D2: I57.7 (O1b), I58.27 (D2), I60.1 (D2), I63.1 (D2)
D3: I57.9 (O0b), I58.28 (D3), I60.2 (D3), I63.40 (D3)
D4: I57.12 (O3a), I58.1 (D4), I60.5 (D4), I63.39 (D4)
D5: I57.14 (O2a), I58.2 (D5), I60.6 (D5), I63.38 (D5)
D6: I57.16 (O1a), I58.3 (D6), I60.7 (D6), I63.3 (D6)
D7: I57.18 (O0a), I58.4 (D7), I60.8 (D7), I63.2 (D7)
DSR: I62.10 (IN_C), M50.1
DTR: I61.8 (3Y), M50.2
FIREINT: I33.9
GND: C15.2, C16.2, C17.2, C18.2, C70.2, I33.7 (GND), I53.6 (Cext), I53.9 (A), I55.12 (GND), I56.5 (EI), I56.8 (GND), I57.2 (I0a), I57.4 (I1a), I57.6 (I2a), I57.8 (I3a), I57.10 (GND), I57.17 (I3b), I58.5 (GND), I60.4 (GND), I61.7 (GND), I62.7 (GND), I63.11 (GND), M1.2, M1.4, M1.6, M1.8, M1.10, M1.12, M1.14, M1.16, M1.18, M1.20, M1.22, M1.24, M1.31, M1.33, M2.3, M2.7, M2.9, M2.13, M13.1, M13.S (Shield)
HARRY: I53.11 (Clr), R46.2
unnamed: C15.1, I62.9 (RC_C)
unnamed: C16.1, I62.5 (RC_B)
unnamed: C17.1, I62.2 (RC_A)
unnamed: C18.1, I53.7 (RCext), R47.2
unnamed: C70.1, I53.10 (B), I63.18 (ARDY)
unnamed: I21.5, I33.3
unnamed: I21.6, I63.24 (IEI)
unnamed: I21.8, I33.4
unnamed: I22.8, I60.25 (~RxC)
unnamed: I22.9, I22.10, I58.8 (TO1)
unnamed: I33.2, I33.5, I58.11 (IEO)
unnamed: I33.6, I55.3 (D1)
unnamed: I33.8, I55.6 (D2)
unnamed: I33.10, I63.22 (IEO)
unnamed: I46.9, I46.10, I54.9, I56.14 (GS)
unnamed: I46.8, I46.12, I46.13, R43.2
unnamed: I53.12 (~Q), M1.1
unnamed: I54.8, I55.4 (E23), I55.13 (E01), I57.1 (OEa), I57.19 (OEb)
unnamed: I55.7 (D3), I56.1 (I4), I56.2 (I5), I56.3 (I6), I56.4 (I7), R42.2
unnamed: I55.9 (Q3), I56.10 (IO)
unnamed: I55.10 (Q2), I56.11 (I1)
unnamed: I55.15 (Q1), I56.12 (I2)
unnamed: I55.16 (Q0), I56.13 (I3)
unnamed: I56.6 (S2), I57.11 (I0b)
unnamed: I56.7 (S1), I57.13 (I1b)
unnamed: I56.9 (S0), I57.15 (I2b)
unnamed: I58.7 (TO0), I60.9 (~TxC)
unnamed: I58.9 (TO2), I58.20 (TRG3)
unnamed: I60.3 (RxD), I62.3 (OUT_A)
unnamed: I60.17 (~CTS), I62.6 (OUT_B)
unnamed: I60.19 (TxD), I61.2 (1A)
unnamed: I60.22 (~DSR), I62.8 (OUT_C)
unnamed: I60.23 (~RTS), I61.5 (2B)
unnamed: I60.24 (~DTR), I61.10 (3B)
unnamed: I61.3 (1Y), M13.3
unnamed: I61.6 (2Y), M13.4
unnamed: I61.4 (2A), I61.9 (3A), I61.12 (4A), I61.13 (4B), R44.2
unnamed: I62.1 (IN_A), M13.5
unnamed: I62.4 (IN_B), M13.2
unnamed: I62.13 (IN_D), R45.2
unnamed: I63.7 (PA7), M1.17
unnamed: I63.8 (PA6), M1.15
unnamed: I63.9 (PA5), M1.13
unnamed: I63.10 (PA4), M1.11
unnamed: I63.12 (PA3), M1.9
unnamed: I63.13 (PA2), M1.7
unnamed: I63.14 (PA1), M1.5
unnamed: I63.15 (PA0), M1.3
unnamed: I63.16 (~ASTB), M1.19, R57.2
unnamed: I63.17 (~BSTB), M2.11, R58.2
unnamed: I63.21 (BRDY), M2.5
unnamed: I63.27 (PB0), M2.2
unnamed: I63.28 (PB1), M2.4
unnamed: I63.29 (PB2), M2.6
unnamed: I63.30 (PB3), M2.8
unnamed: I63.31 (PB4), M2.10
unnamed: I63.32 (PB5), M2.12
unnamed: I63.33 (PB6), M2.14
unnamed: I63.34 (PB7), M2.16
PE: M1.23
RESET: I60.21 (RESET)
SYSCLK: I58.15 (CLK), I63.25 (CLK)
~ADCINT: I21.9, I33.1
~CTC: I58.16 (~CE)
~ERR: M1.28
~INA: I54.3, I54.10
~INT: I46.11, I58.12 (~INT), I63.23 (~INT)
~IORQ: I54.1, I58.10 (~IORQ), I63.36 (~IORQ)
~KYBDINT: I55.2 (D0), I58.13 (IEI)
~M1: I54.2, I58.14 (~M1), I63.37 (~M1)
~PCI: I60.11 (~CS)
~PIO: I63.4 (~CE)
~RD: I58.6 (~RD), I60.13 (~RD), I63.35 (~RD)
~RESET: I58.17 (~RESET)
~WR: I60.10 (~WR)

Notes on the sheet:
Why do it this way?
