Board-Folk/Einstein-TC-01/Kicad/einstein_vdp.kicad_sch

## KiCad design Kicad/einstein_vdp.kicad_sch (2025-11-02)

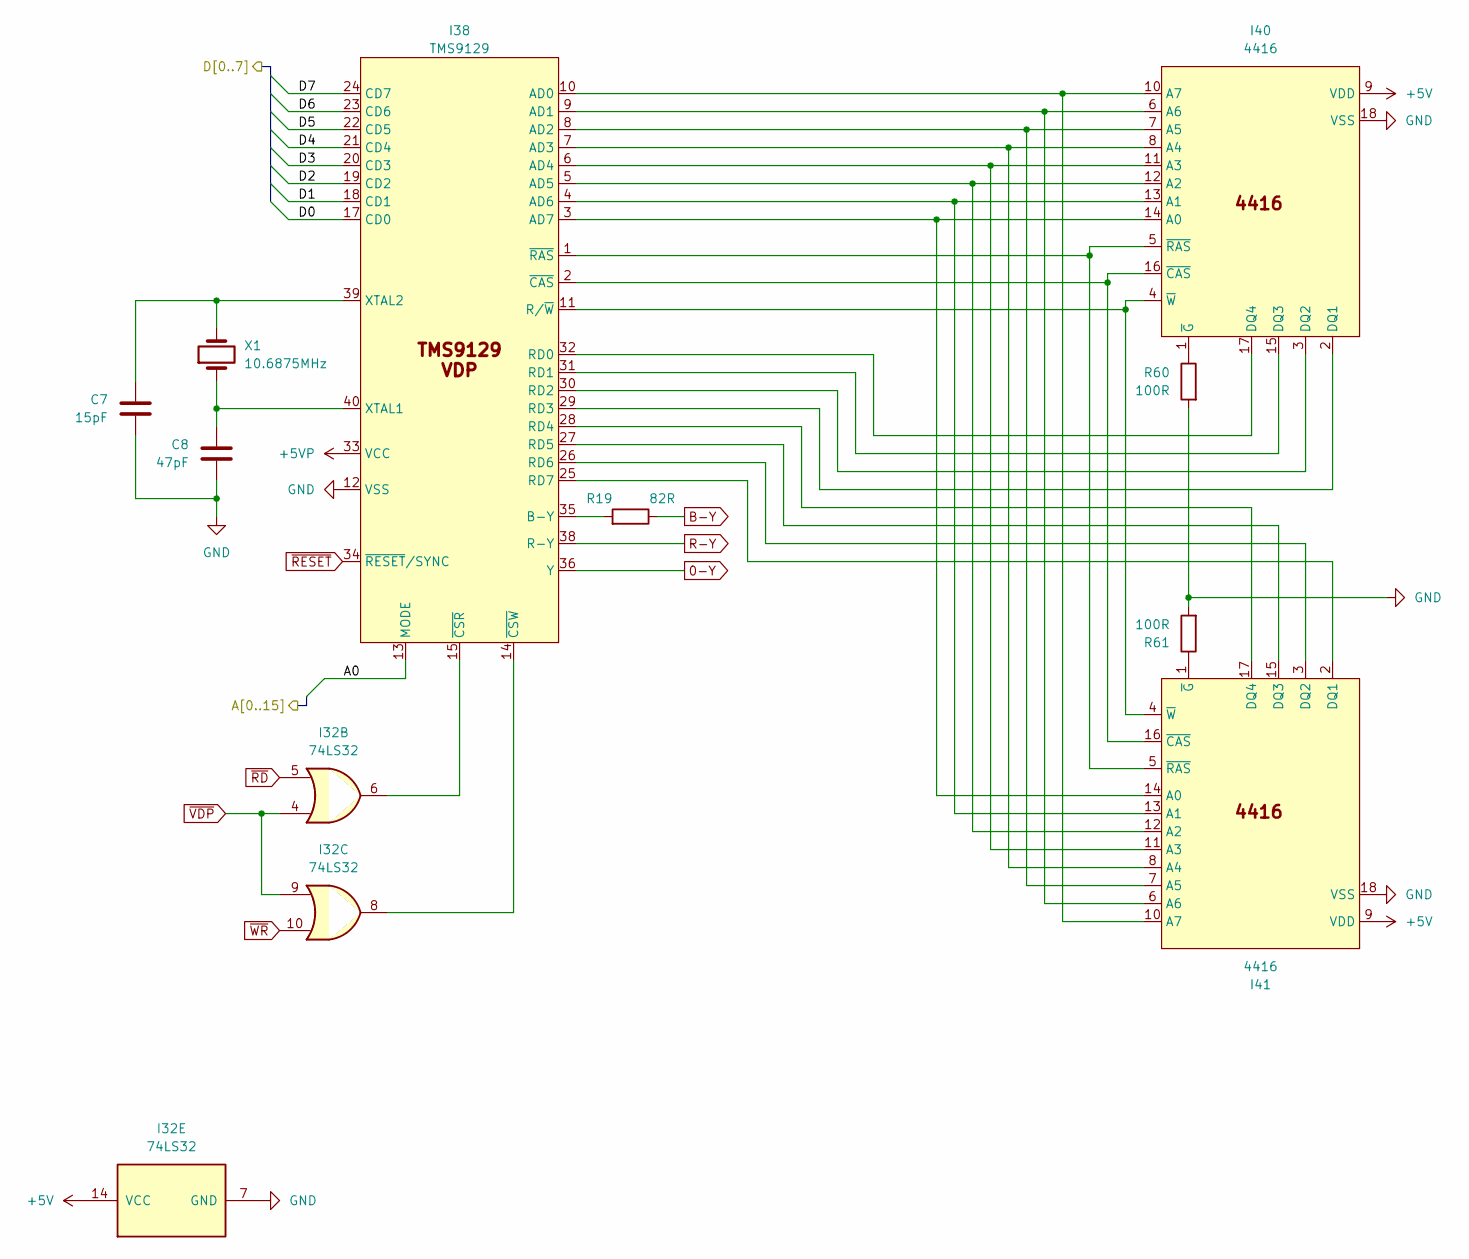
[picture p51: schematic einstein_vdp.kicad_sch]

Parts:
C7: 15pF; C_Disc_12.7mm
C8: 47pF; C_Disc_12.7mm
I32: 74LS32; DIP-14_W7.62mm
I38: TMS9129; DIP-40_W15.24mm
I40, I41: 4416; DIP-18_W7.62mm
R19: 82R; Resistor 12.70mm
R60, R61: 100R; Resistor 12.70mm
X1: 10.6875MHz; Crystal

Connections:
0-Y: I38.36 (Y)
+5V: I32.14 (VCC), I40.9 (VDD), I41.9 (VDD)
+5VP: I38.33 (VCC)
A0: I38.13 (MODE)
B-Y: R19.1
D0: I38.17 (CD0)
D1: I38.18 (CD1)
D2: I38.19 (CD2)
D3: I38.20 (CD3)
D4: I38.21 (CD4)
D5: I38.22 (CD5)
D6: I38.23 (CD6)
D7: I38.24 (CD7)
GND: C7.2, C8.2, I32.7 (GND), I38.12 (VSS), I40.18 (VSS), I41.18 (VSS), R60.2, R61.2
unnamed: C7.1, I38.39 (XTAL2), X1.2
unnamed: C8.1, I38.40 (XTAL1), X1.1
unnamed: I32.6, I38.15 (~CSR)
unnamed: I32.8, I38.14 (~CSW)
unnamed: I38.1 (~RAS), I40.5 (~RAS), I41.5 (~RAS)
unnamed: I38.2 (~CAS), I40.16 (~CAS), I41.16 (~CAS)
unnamed: I38.3 (AD7), I40.14 (A0), I41.14 (A0)
unnamed: I38.4 (AD6), I40.13 (A1), I41.13 (A1)
unnamed: I38.5 (AD5), I40.12 (A2), I41.12 (A2)
unnamed: I38.6 (AD4), I40.11 (A3), I41.11 (A3)
unnamed: I38.7 (AD3), I40.8 (A4), I41.8 (A4)
unnamed: I38.8 (AD2), I40.7 (A5), I41.7 (A5)
unnamed: I38.9 (AD1), I40.6 (A6), I41.6 (A6)
unnamed: I38.10 (AD0), I40.10 (A7), I41.10 (A7)
unnamed: I38.11 (R/~W), I40.4 (~W), I41.4 (~W)
unnamed: I38.25 (RD7), I41.2 (DQ1)
unnamed: I38.26 (RD6), I41.3 (DQ2)
unnamed: I38.27 (RD5), I41.15 (DQ3)
unnamed: I38.28 (RD4), I41.17 (DQ4)
unnamed: I38.29 (RD3), I40.2 (DQ1)
unnamed: I38.30 (RD2), I40.3 (DQ2)
unnamed: I38.31 (RD1), I40.15 (DQ3)
unnamed: I38.32 (RD0), I40.17 (DQ4)
unnamed: I38.35 (B-Y), R19.2
unnamed: I40.1 (~G), R60.1
unnamed: I41.1 (~G), R61.1
R-Y: I38.38 (R-Y)
~RD: I32.5
~RESET: I38.34 (~RESET/SYNC)
~VDP: I32.4, I32.9
~WR: I32.10
