Board-Folk/Einstein-TC-01/Kicad/einstein_videoout.kicad_sch

## KiCad design Kicad/einstein_videoout.kicad_sch (2026-03-14)

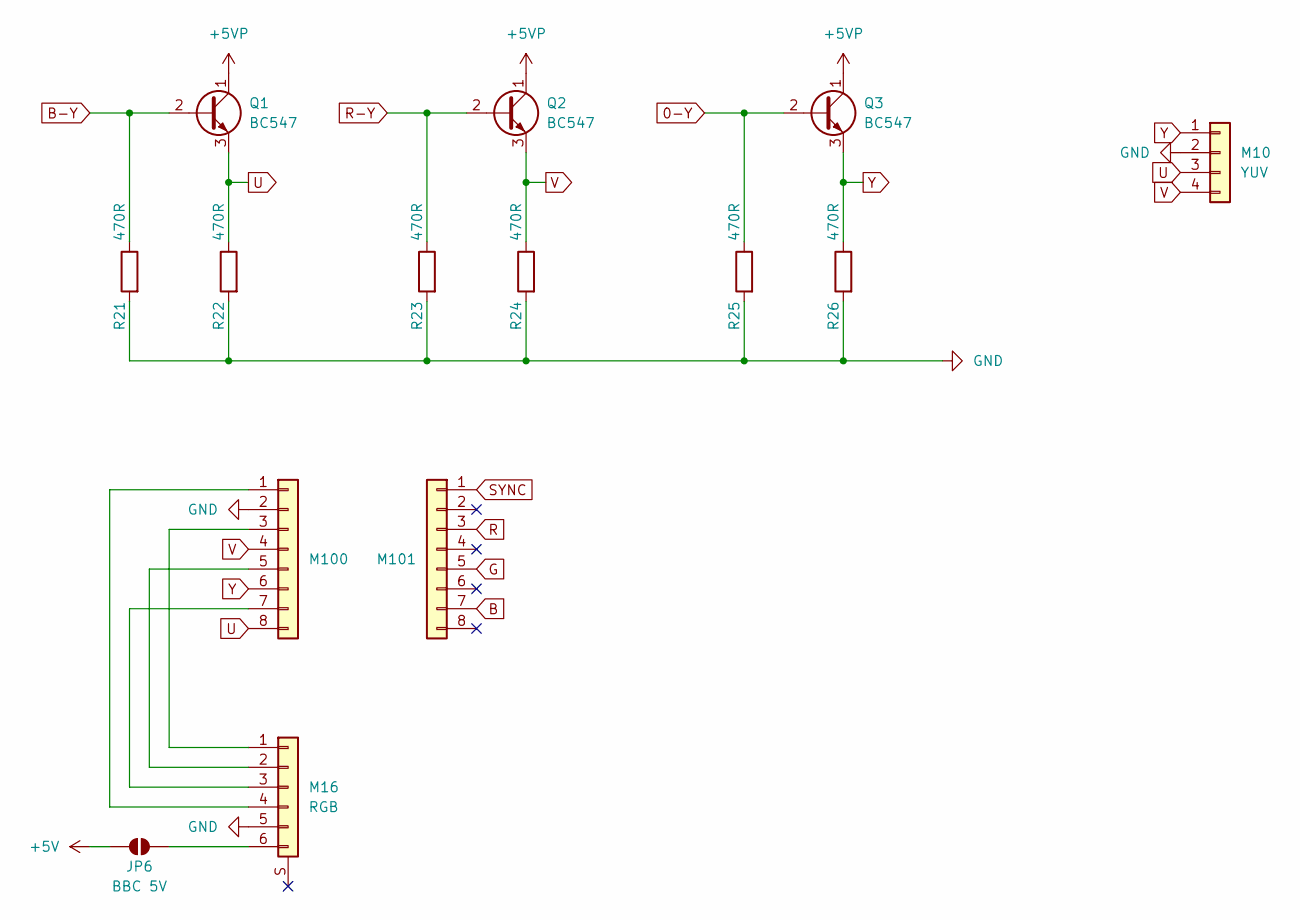
[picture p52: schematic einstein_videoout.kicad_sch]

Parts:
JP6: BBC 5V; BBC Bodge
M10: YUV; M10 PinHeader_1x04_P2.54mm
M16: RGB; DIN6
M100, M101: M PinHeader_1x08_P2.54mm
Q1, Q2, Q3: BC547; Transistor - Box 2
R21, R22, R23, R24, R25, R26: 470R; Resistor 12.70mm

Connections:
0-Y: Q3.2 (B), R25.1
+5V: JP6.1 (A)
+5VP: Q1.1 (C), Q2.1 (C), Q3.1 (C)
B: M101.7
B-Y: Q1.2 (B), R21.1
G: M101.5
GND: M10.2, M16.5, M100.2, R21.2, R22.2, R23.2, R24.2, R25.2, R26.2
unnamed: JP6.2 (B), M16.6
unnamed: M16.4, M100.1
unnamed: M16.1, M100.3
unnamed: M16.2, M100.5
unnamed: M16.3, M100.7
R: M101.3
R-Y: Q2.2 (B), R23.1
SYNC: M101.1
U: M10.3, M100.8, Q1.3 (E), R22.1
V: M10.4, M100.4, Q2.3 (E), R24.1
Y: M10.1, M100.6, Q3.3 (E), R26.1
